Slicit/Roxanne/sources/stl/rev1/X_Carriage_v3.STL

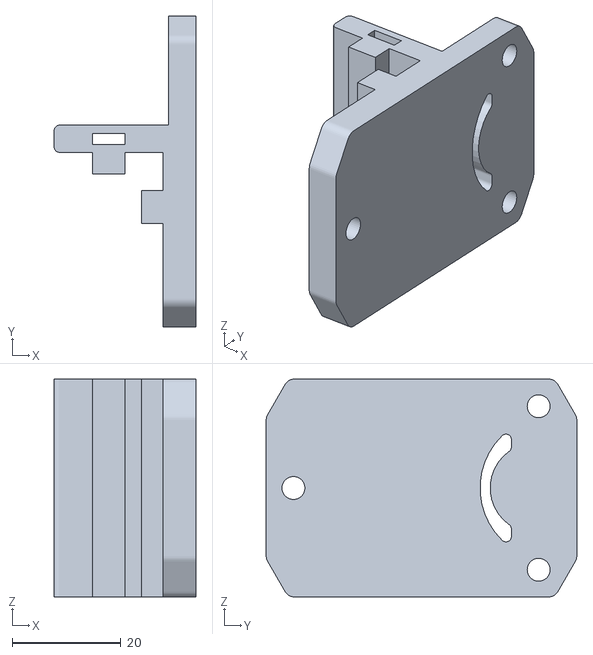
[picture p15: CAD file, 2013-07-26]
sources/stl/rev1/X_Carriage_v3.STL
26.0 x 57.0 x 40.0
