Slicit/Roxanne/sources/solidworks/X-End_Motor_Adj_V2.SLDPRT

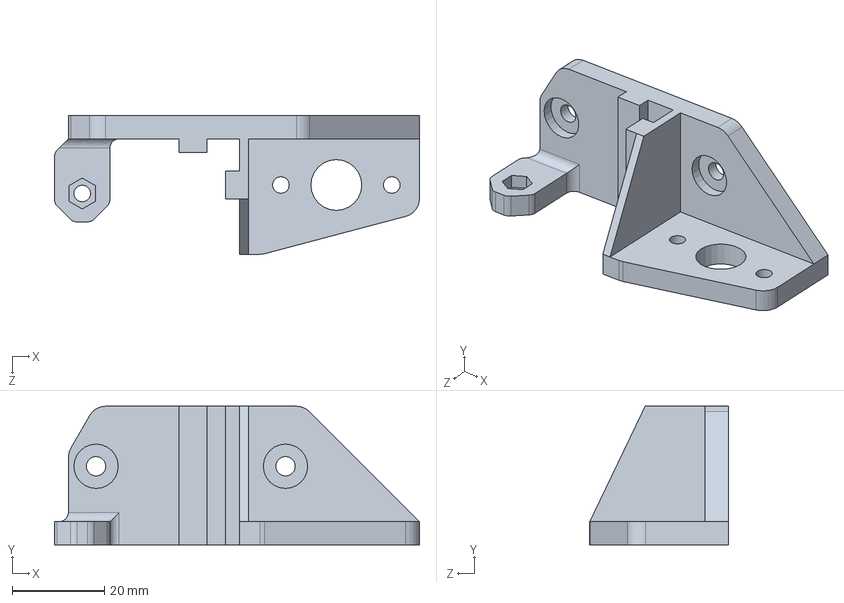
[picture p16: CAD file, 2013-10-02]
sources/solidworks/X-End_Motor_Adj_V2.SLDPRT
79.0 x 30.0 x 30.0 mm
