Slicit/Roxanne/sources/stl/(2)Pulley_T25_624ZZ.stl

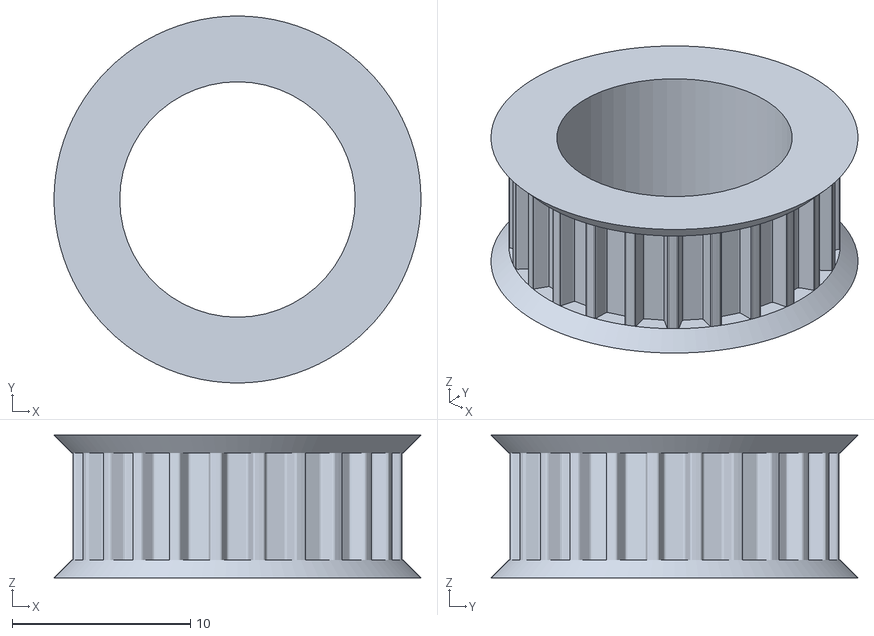
[picture p17: CAD file, 2013-10-02]
sources/stl/(2)Pulley_T25_624ZZ.stl
20.6 x 20.6 x 8.00
