Slicit/Roxanne/sources/stl/rev1/Triple_Fan_Holder.STL

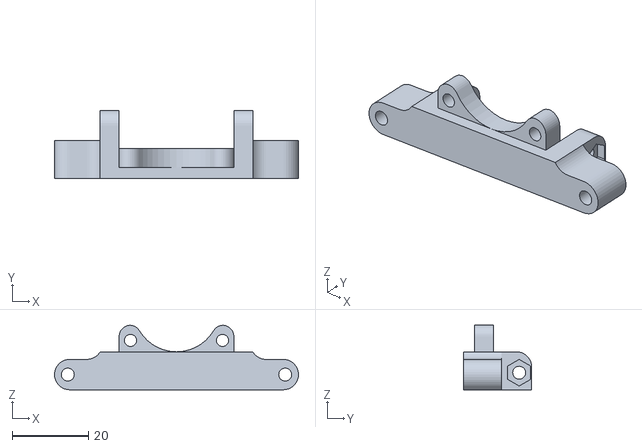
[picture p19: CAD file, 2013-07-26]
sources/stl/rev1/Triple_Fan_Holder.STL
64.2 x 18.0 x 17.0
