Slicit/Roxanne/sources/solidworks/X-End-Idler-V2.SLDPRT

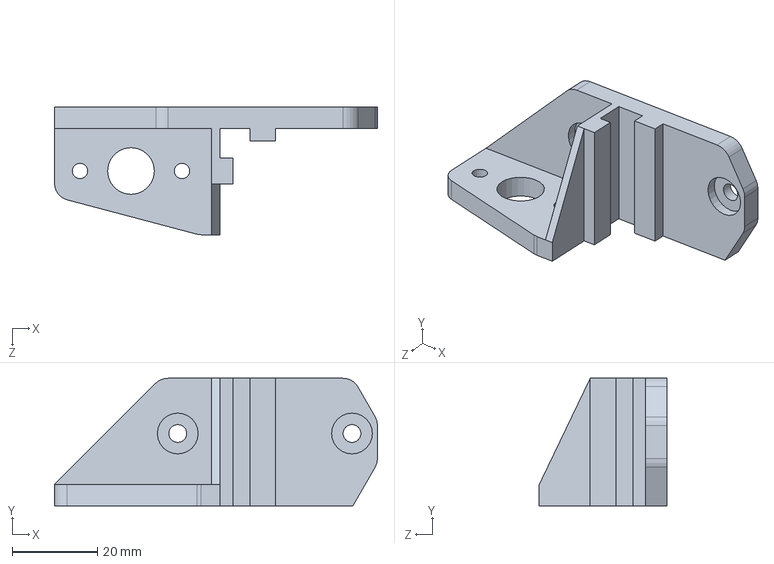
[picture p20: CAD file, 2013-10-02]
sources/solidworks/X-End-Idler-V2.SLDPRT
76.0 x 30.0 x 30.0 mm
