Slicit/Roxanne/sources/stl/rev1/Bowden_JHead_V2.STL

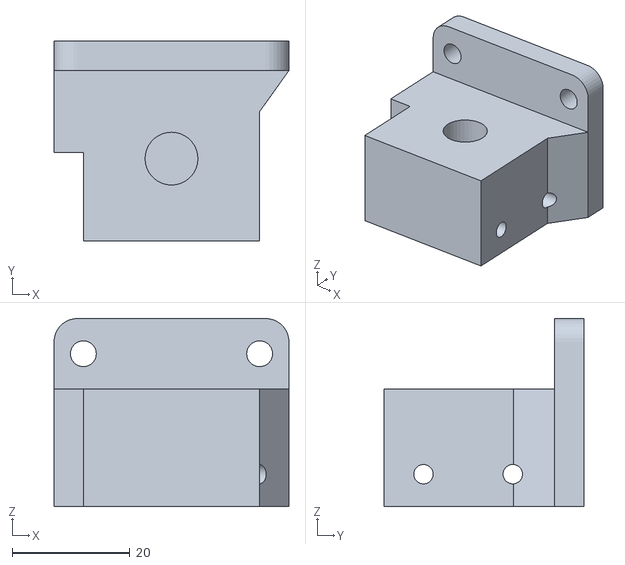
[picture p21: CAD file, 2013-07-26]
sources/stl/rev1/Bowden_JHead_V2.STL
40.0 x 34.0 x 32.0
