Slicit/Roxanne/sources/solidworks/EndstopY.SLDPRT

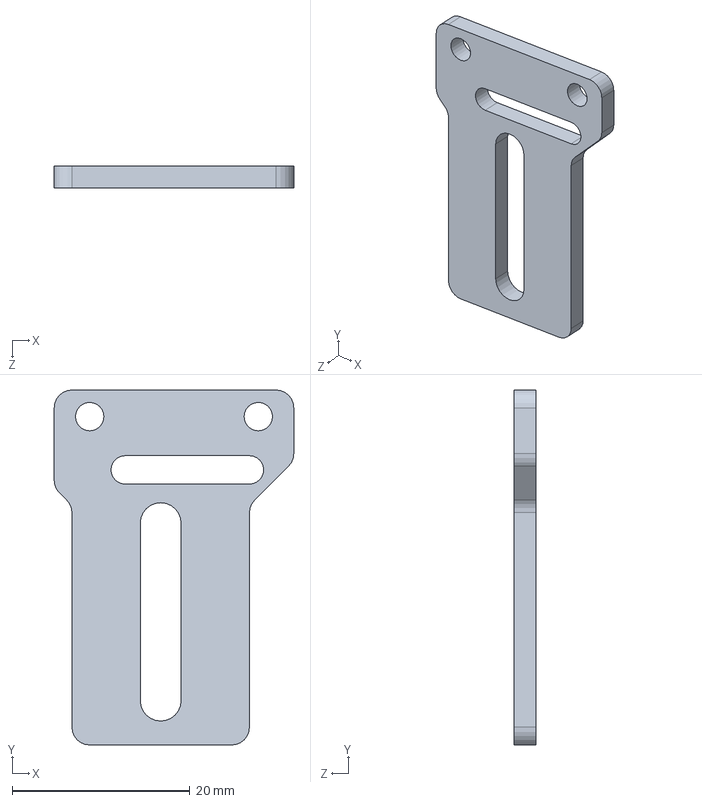
[picture p22: CAD file, 2013-10-02]
sources/solidworks/EndstopY.SLDPRT
27.0 x 40.0 x 2.50 mm
