Slicit/Roxanne/sources/stl/rev1/Glass_Holder.STL

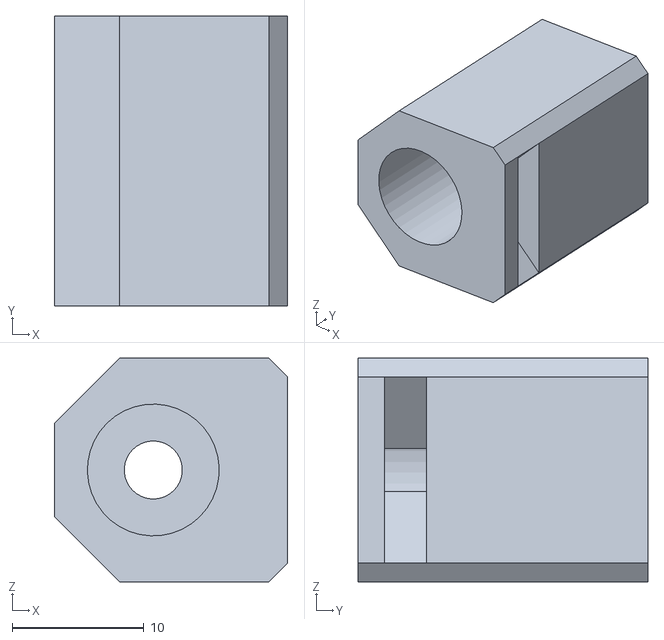
[picture p23: CAD file, 2013-07-24]
sources/stl/rev1/Glass_Holder.STL
17.7 x 22.0 x 17.0
