Slicit/Roxanne/sources/stl/rev1/Axe_Guide_160mm.STL

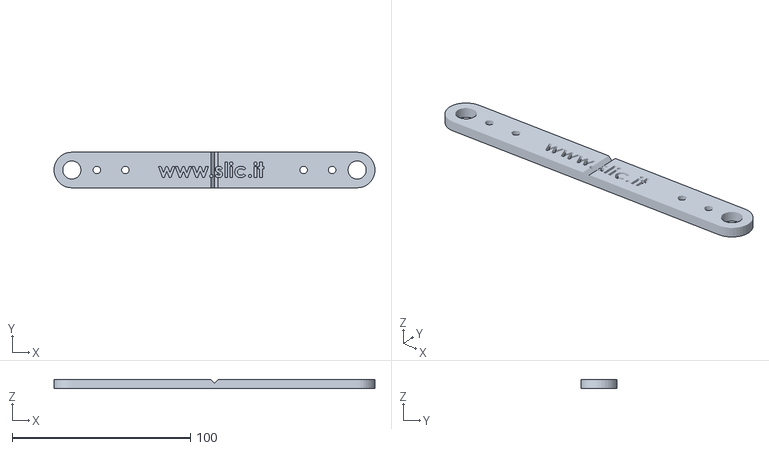
[picture p24: CAD file, 2013-07-24]
sources/stl/rev1/Axe_Guide_160mm.STL
180.0 x 20.0 x 5.00
