Slicit/Roxanne/sources/solidworks/Angle_Holder.SLDPRT

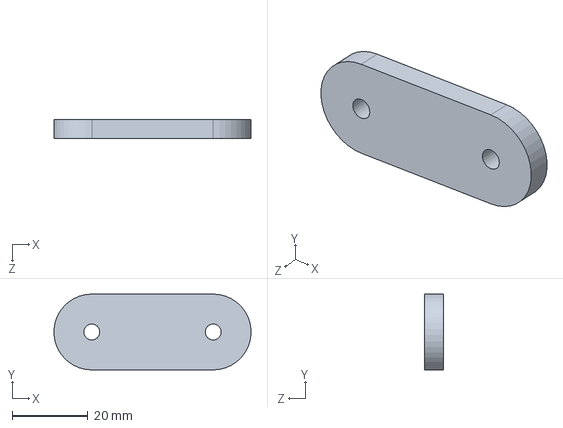
[picture p25: CAD file, 2013-09-25]
sources/solidworks/Angle_Holder.SLDPRT
51.9 x 20.0 x 5.00 mm
