Slicit/Roxanne/sources/stl/(1)Y-Endstop-Holder.STL

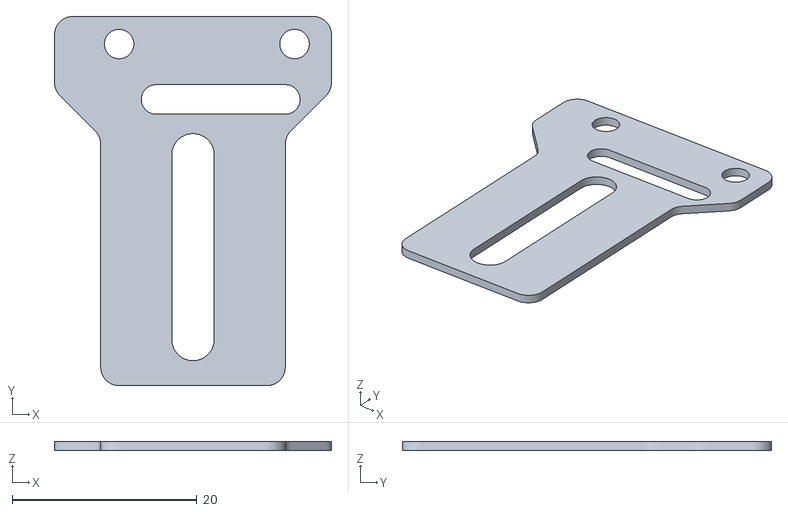
[picture p26: CAD file, 2013-09-25]
sources/stl/(1)Y-Endstop-Holder.STL
30.0 x 40.0 x 1.00
