Slicit/Roxanne/sources/stl/rev1/Y_Motor_Bottom.STL

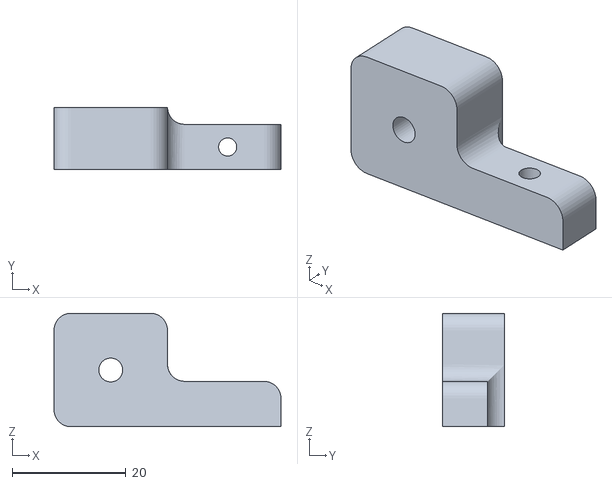
[picture p27: CAD file, 2013-07-10]
sources/stl/rev1/Y_Motor_Bottom.STL
40.0 x 11.0 x 20.0
