Slicit/Roxanne/sources/solidworks/Charn_Type_1.SLDPRT

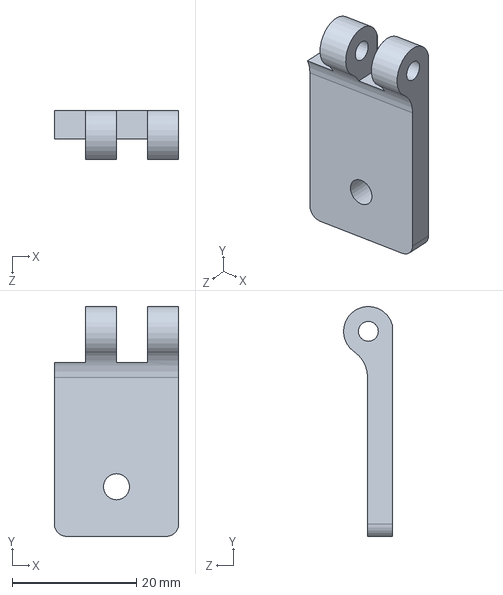
[picture p28: CAD file, 2013-09-25]
sources/solidworks/Charn_Type_1.SLDPRT
20.0 x 37.0 x 7.87 mm
