Slicit/Roxanne/sources/stl/(8)Nut_Holder_Leveller.STL

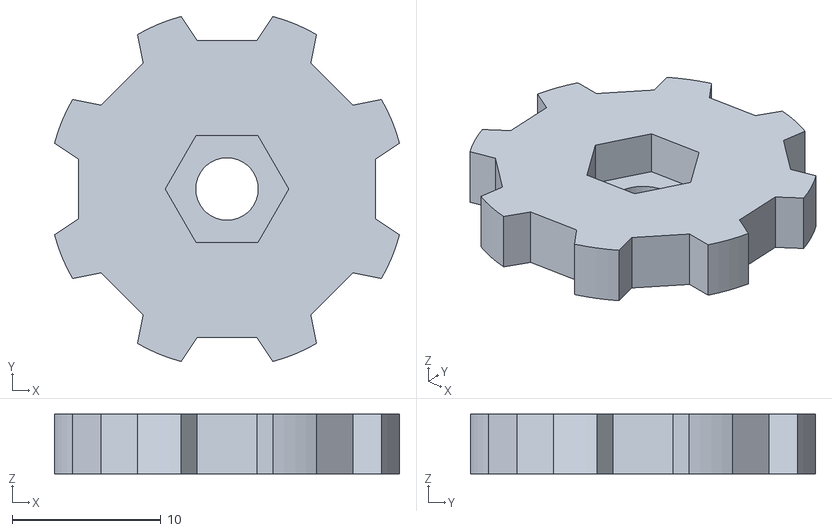
[picture p29: CAD file, 2013-09-25]
sources/stl/(8)Nut_Holder_Leveller.STL
23.2 x 23.2 x 4.00
