Slicit/Roxanne/sources/stl/rev1/Y_Motor_Top.STL

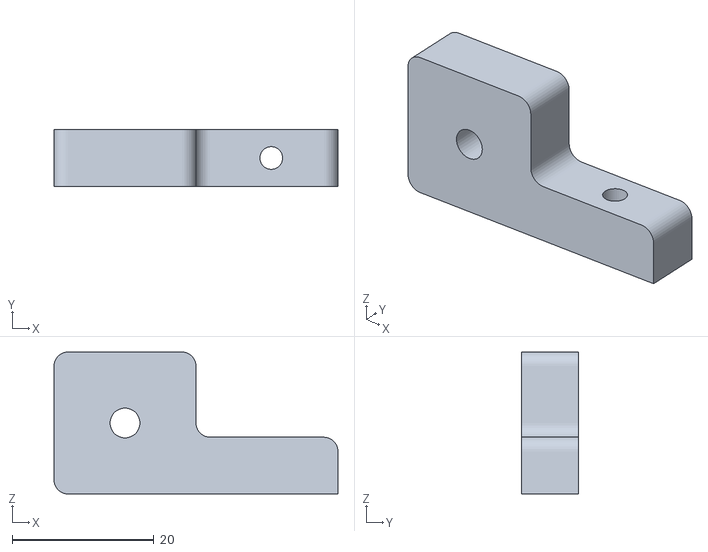
[picture p30: CAD file, 2013-07-10]
sources/stl/rev1/Y_Motor_Top.STL
40.0 x 8.00 x 20.0
