Slicit/Roxanne/sources/solidworks/Spacer_Y_Endstop_2.SLDPRT

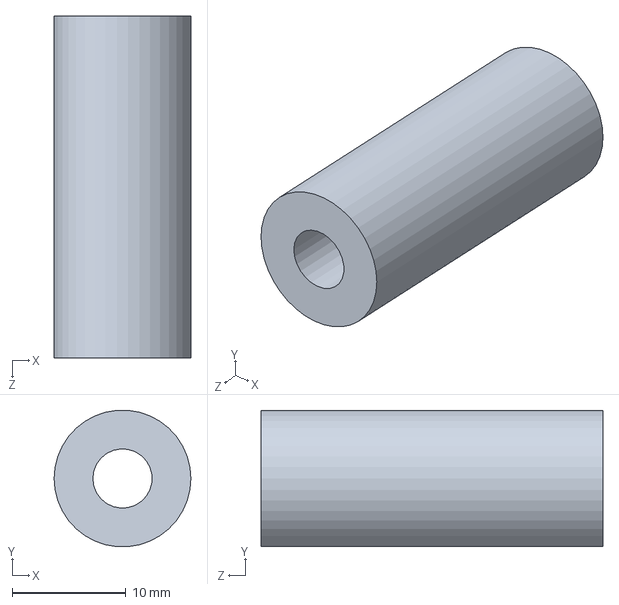
[picture p31: CAD file, 2013-09-25]
sources/solidworks/Spacer_Y_Endstop_2.SLDPRT
12.0 x 12.0 x 30.0 mm
