Slicit/Roxanne/sources/stl/(4)Glass_Holder.STL

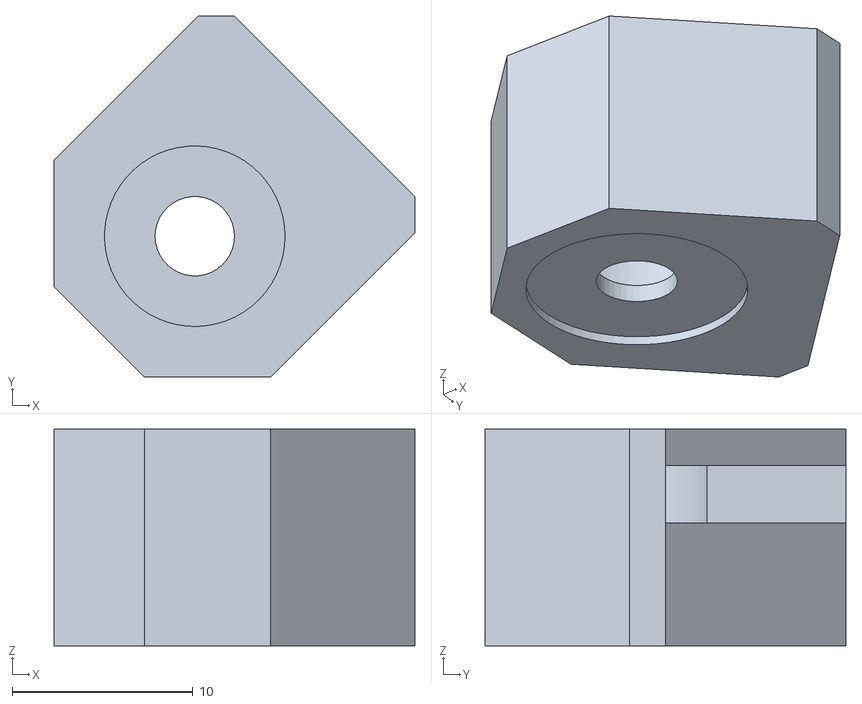
[picture p32: CAD file, 2013-09-25]
sources/stl/(4)Glass_Holder.STL
20.0 x 20.0 x 12.0
