Slicit/Roxanne/sources/stl/(1)X-Carriage.STL

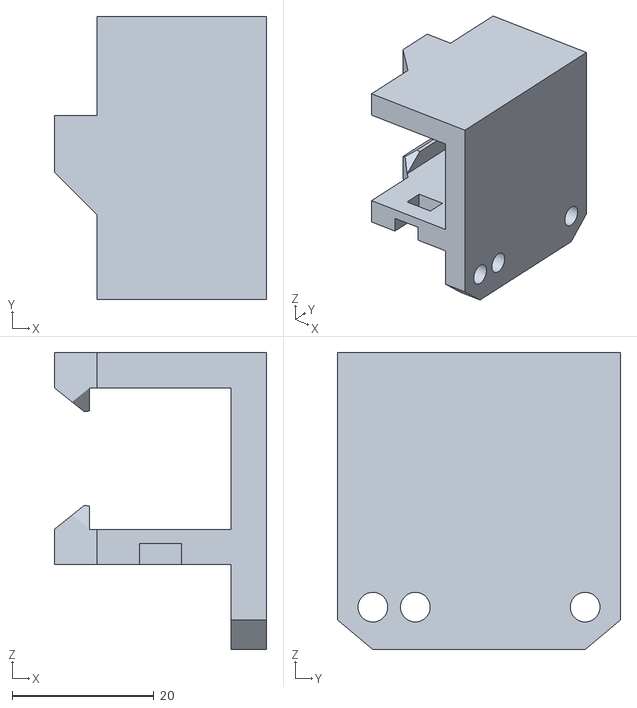
[picture p33: CAD file, 2013-09-25]
sources/stl/(1)X-Carriage.STL
30.0 x 40.0 x 42.0
