Slicit/Roxanne/sources/stl/(1)Y-Endstop-Spacer.STL

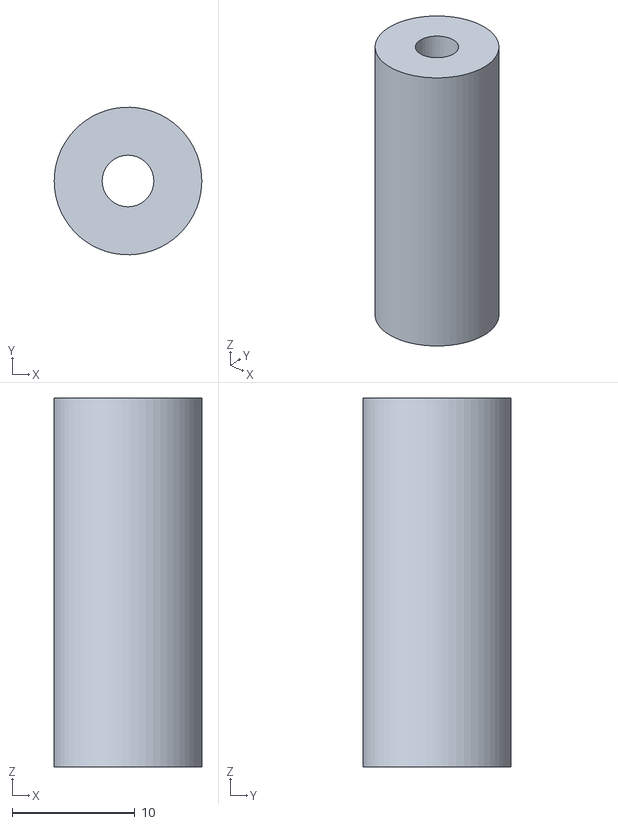
[picture p34: CAD file, 2013-09-25]
sources/stl/(1)Y-Endstop-Spacer.STL
12.0 x 12.0 x 30.0
