Slicit/Roxanne/sources/stl/rev1/LM10UU_Holder_Higher.STL

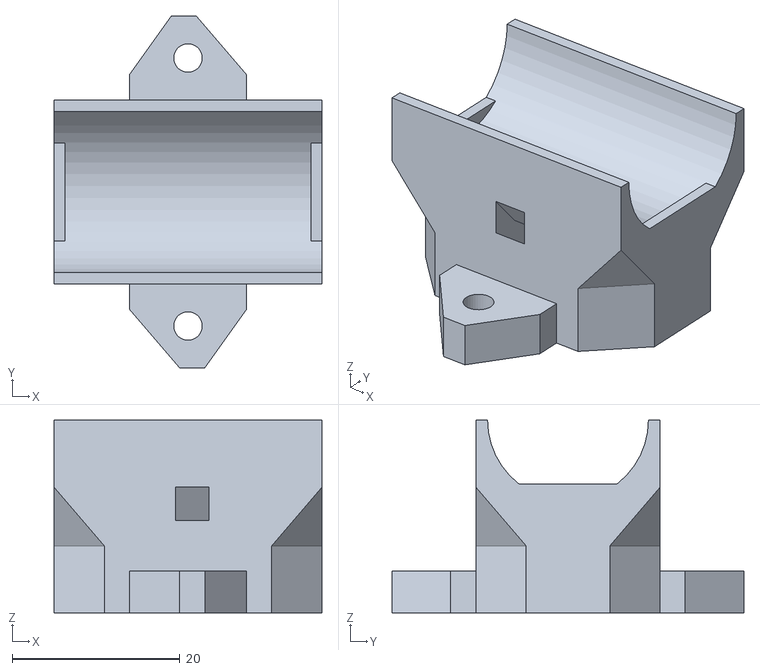
[picture p35: CAD file, 2013-06-12]
sources/stl/rev1/LM10UU_Holder_Higher.STL
32.0 x 42.0 x 23.0
