Slicit/Roxanne/sources/stl/(1)X-Endstop-Holder.STL

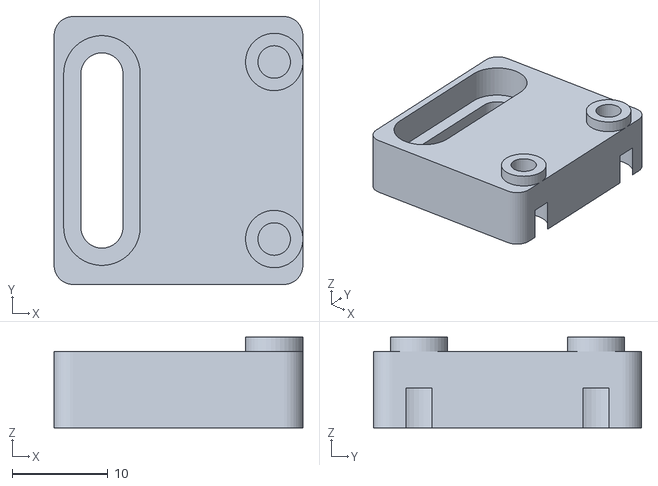
[picture p36: CAD file, 2013-09-25]
sources/stl/(1)X-Endstop-Holder.STL
26.0 x 28.0 x 9.50
