Slicit/Roxanne/sources/stl/rev1/Axe_Guide_160mm_Bearing.STL

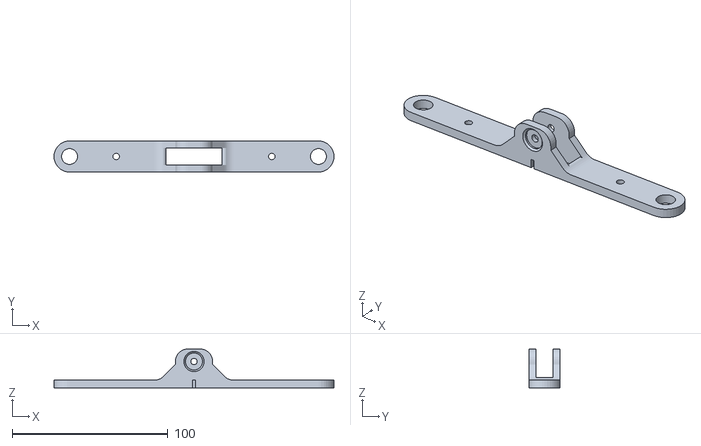
[picture p37: CAD file, 2013-06-12]
sources/stl/rev1/Axe_Guide_160mm_Bearing.STL
180.0 x 20.0 x 25.0
