Slicit/Roxanne/sources/stl/Fans.STL

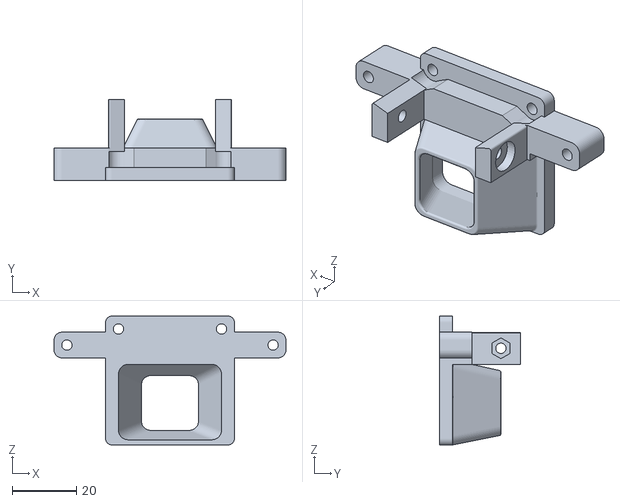
[picture p38: CAD file, 2013-09-23]
sources/stl/Fans.STL
72.0 x 25.0 x 40.0
