Slicit/Roxanne/sources/solidworks/Nema17_48mm.SLDPRT

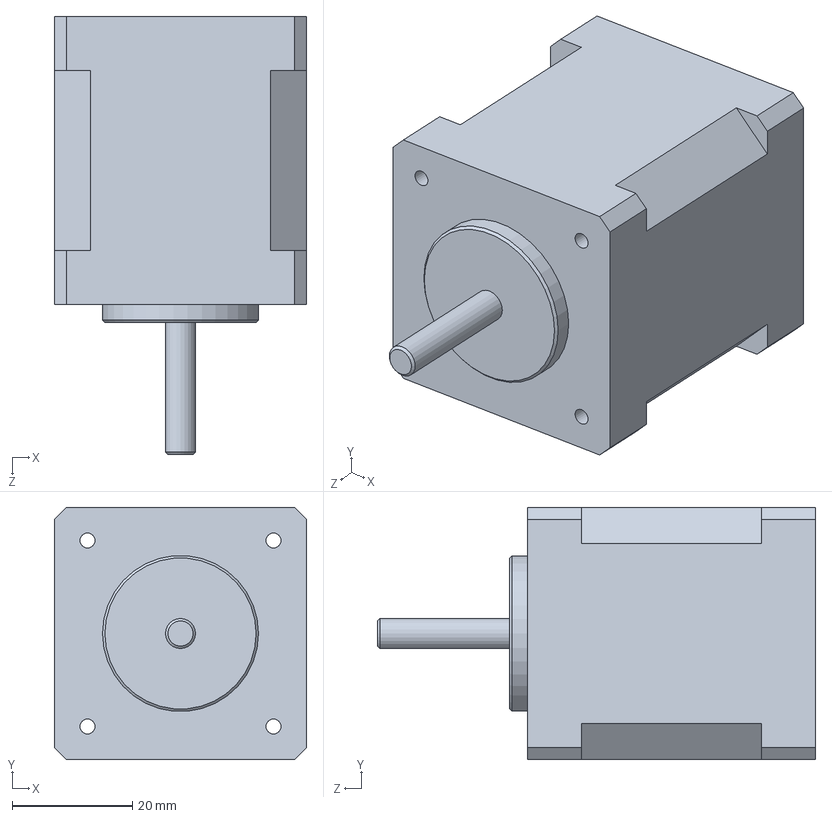
[picture p39: CAD file, 2013-09-25]
sources/solidworks/Nema17_48mm.SLDPRT
42.0 x 42.0 x 73.0 mm
