Slicit/Roxanne/sources/stl/(1)Power-Switch-Plate.STL

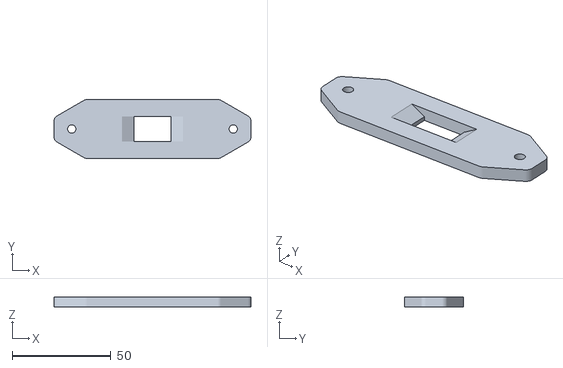
[picture p40: CAD file, 2013-09-23]
sources/stl/(1)Power-Switch-Plate.STL
100.0 x 30.0 x 5.00
