Slicit/Roxanne/sources/stl/rev1/Direct_Drive_Extruder_v3.STL

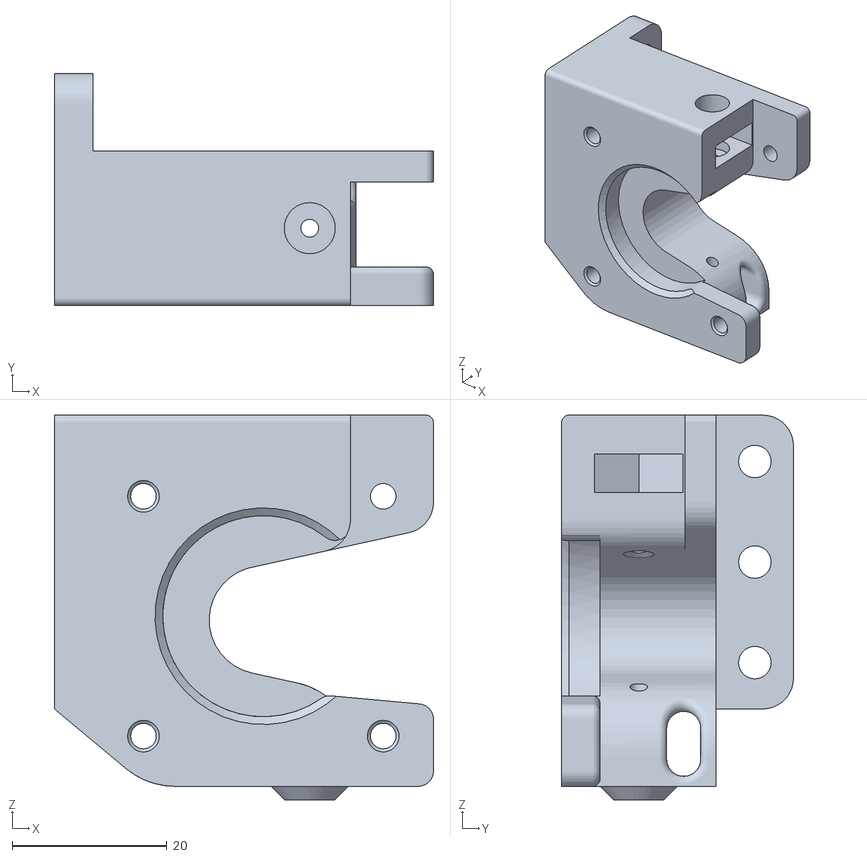
[picture p41: CAD file, 2013-06-11]
sources/stl/rev1/Direct_Drive_Extruder_v3.STL
49.0 x 30.0 x 49.8
