Slicit/Roxanne/sources/stl/rev1/Fan_Support_40mm_Model_2.STL

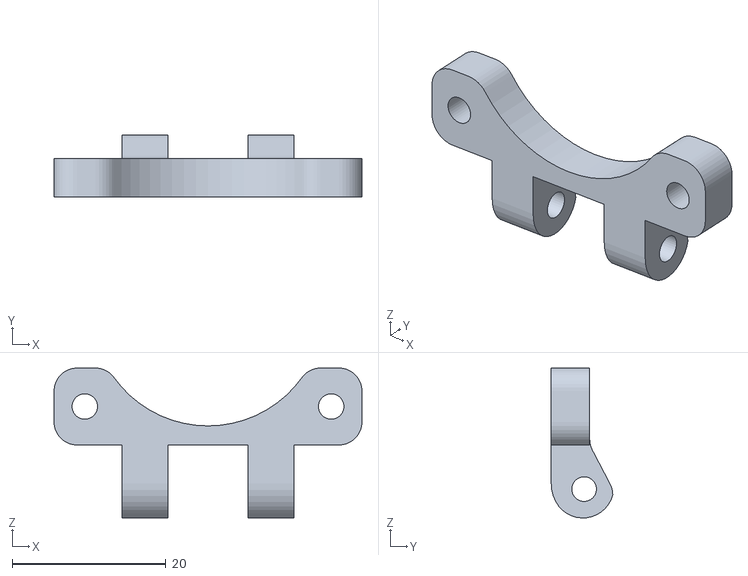
[picture p42: CAD file, 2013-05-20]
sources/stl/rev1/Fan_Support_40mm_Model_2.STL
40.0 x 8.00 x 19.5
