Slicit/Roxanne/sources/stl/rev1/Fan_Support_40mm_Model_1.STL

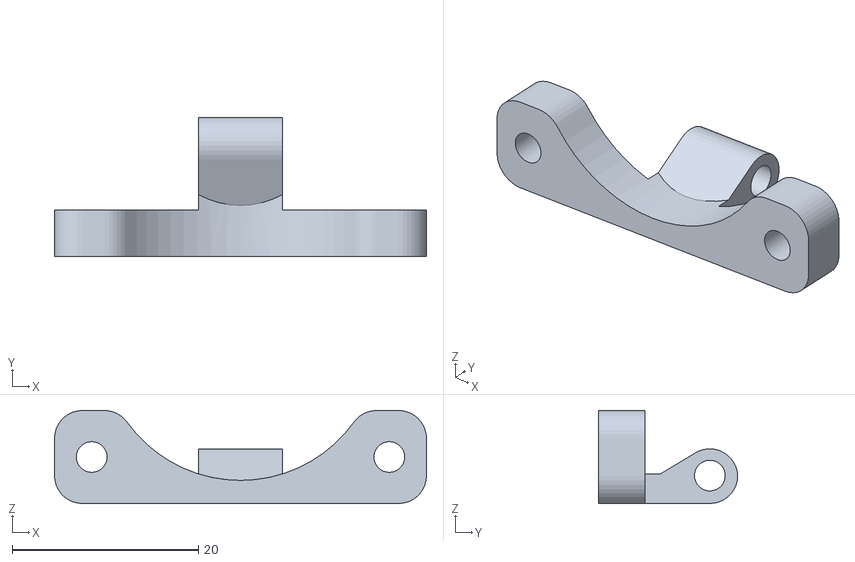
[picture p43: CAD file, 2013-05-20]
sources/stl/rev1/Fan_Support_40mm_Model_1.STL
40.0 x 15.0 x 10.00
