Slicit/Roxanne/sources/solidworks/X-End-Motor-V1.SLDPRT

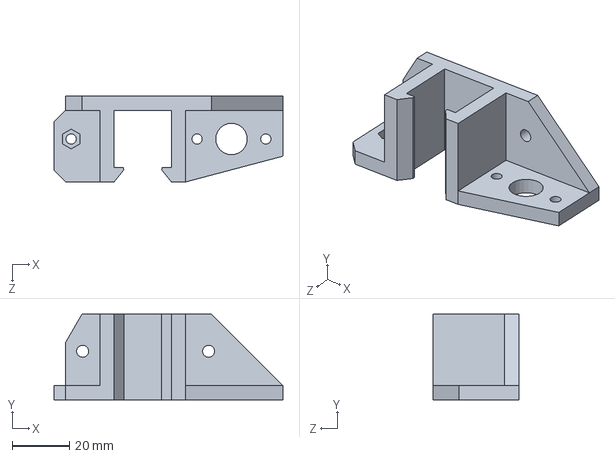
[picture p44: CAD file, 2013-09-25]
sources/solidworks/X-End-Motor-V1.SLDPRT
80.0 x 30.0 x 30.0 mm
