Slicit/Roxanne/sources/stl/rev1/Dual_Extruder_Jhead.stl

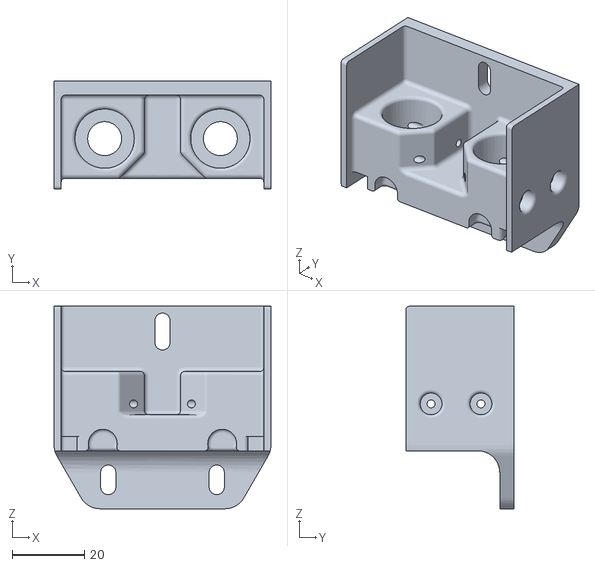
[picture p45: CAD file, 2013-05-20]
sources/stl/rev1/Dual_Extruder_Jhead.stl
60.0 x 30.0 x 56.0
