Slicit/Roxanne/sources/stl/rev1/Fan_Holder.STL

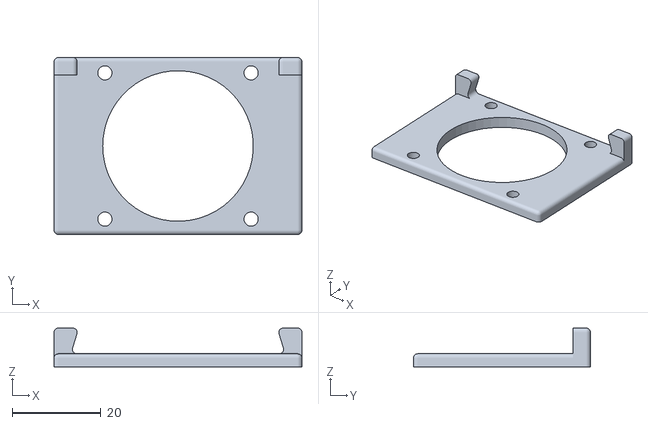
[picture p46: CAD file, 2013-05-20]
sources/stl/rev1/Fan_Holder.STL
56.0 x 40.0 x 8.80
