Slicit/Roxanne/sources/solidworks/Fan_40mm.SLDPRT

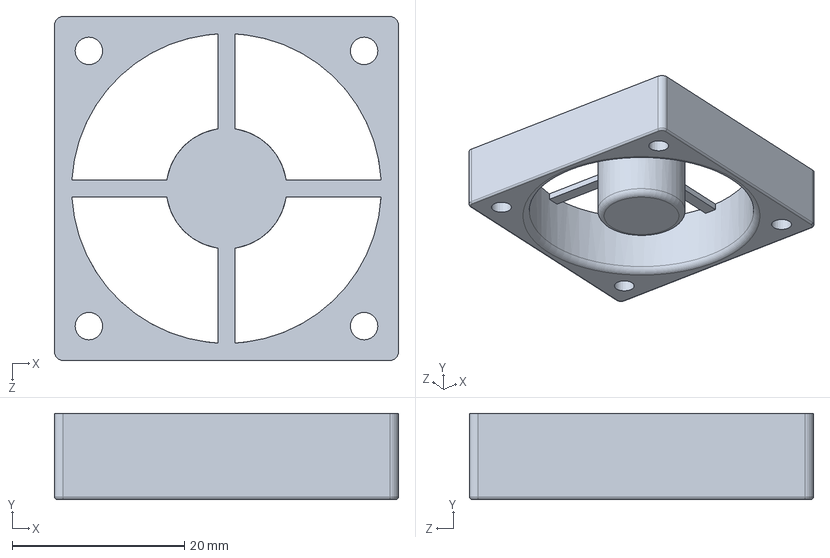
[picture p47: CAD file, 2013-09-23]
sources/solidworks/Fan_40mm.SLDPRT
40.0 x 10.0 x 40.0 mm
