Slicit/Roxanne/sources/stl/rev1/Direct_Drive_Tightner.stl

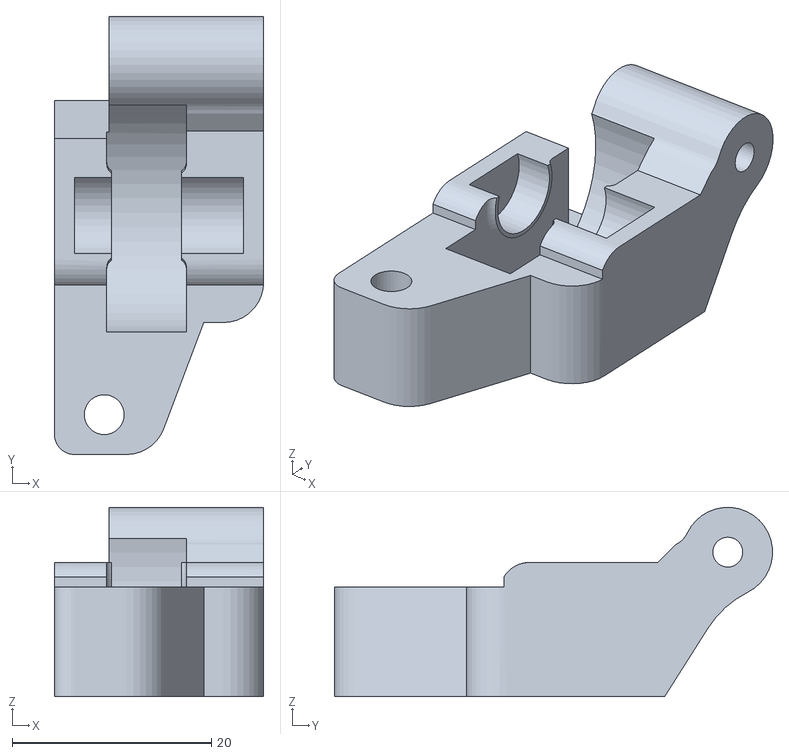
[picture p48: CAD file, 2013-05-19]
sources/stl/rev1/Direct_Drive_Tightner.stl
21.0 x 44.0 x 19.0
