Slicit/Roxanne/sources/solidworks/Mirror_Build_Plate.SLDPRT

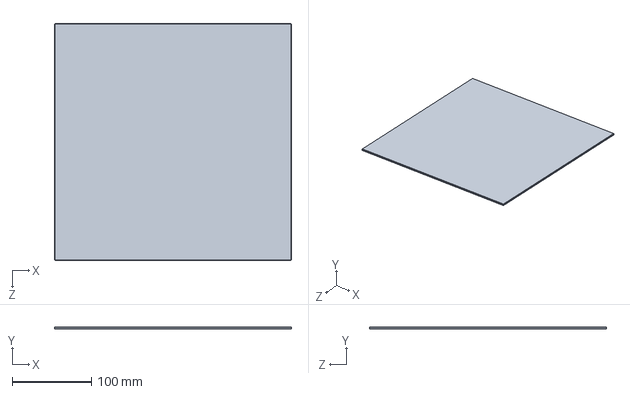
[picture p49: CAD file, 2013-09-23]
sources/solidworks/Mirror_Build_Plate.SLDPRT
300.0 x 3.00 x 300.0 mm
