Slicit/Roxanne/sources/stl/rev1/Rotary_LCD.STL

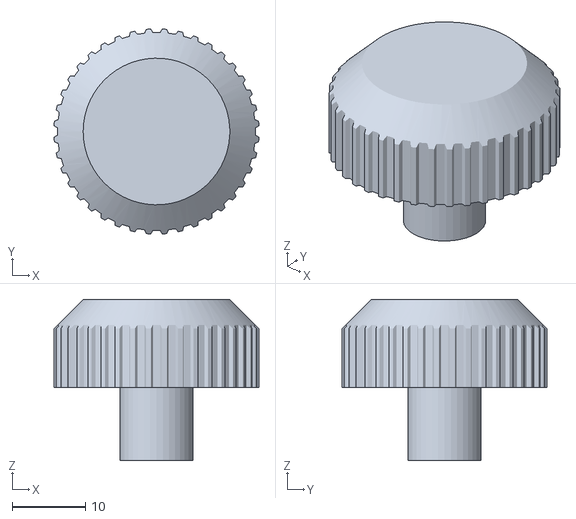
[picture p50: CAD file, 2013-05-19]
sources/stl/rev1/Rotary_LCD.STL
28.0 x 28.0 x 22.0
