Slicit/Roxanne/sources/stl/rev1/X_End_Idler.STL

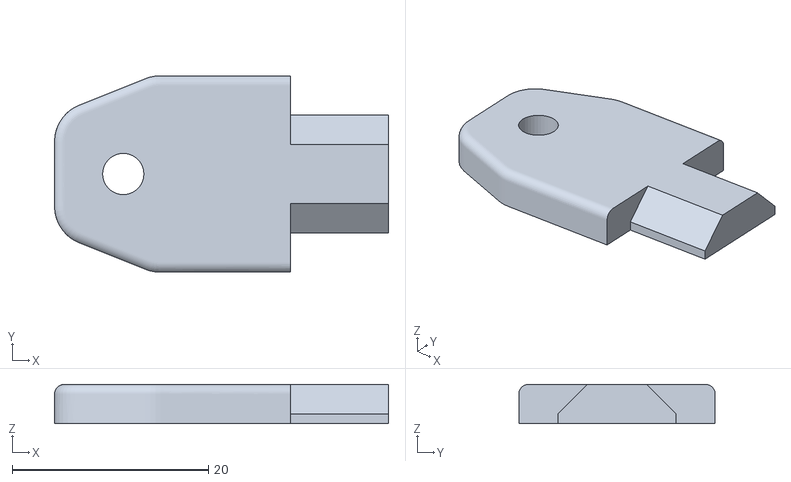
[picture p51: CAD file, 2013-05-19]
sources/stl/rev1/X_End_Idler.STL
34.0 x 20.0 x 4.00
