Slicit/Roxanne/sources/stl/rev1/X_Motor_Plate.STL

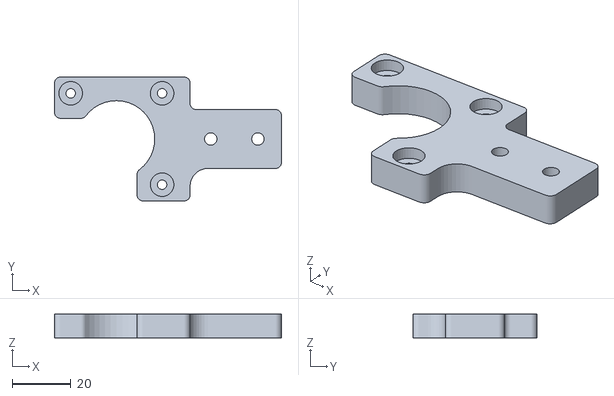
[picture p52: CAD file, 2013-05-18]
sources/stl/rev1/X_Motor_Plate.STL
77.0 x 42.0 x 8.00
