Slicit/Roxanne/sources/stl/rev1/Endstop_Nopcb_Holder_Profile_Y.STL

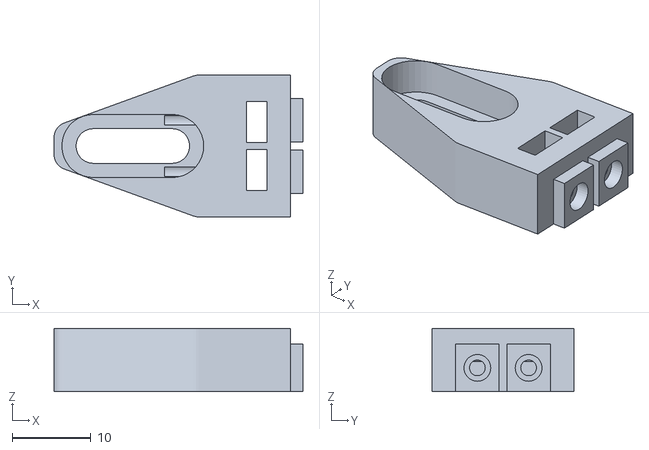
[picture p53: CAD file, 2013-05-15]
sources/stl/rev1/Endstop_Nopcb_Holder_Profile_Y.STL
31.6 x 18.0 x 8.00
