Slicit/Roxanne/sources/stl/rev1/Endstop_Nopcb_Holder_Profile_XZ.STL

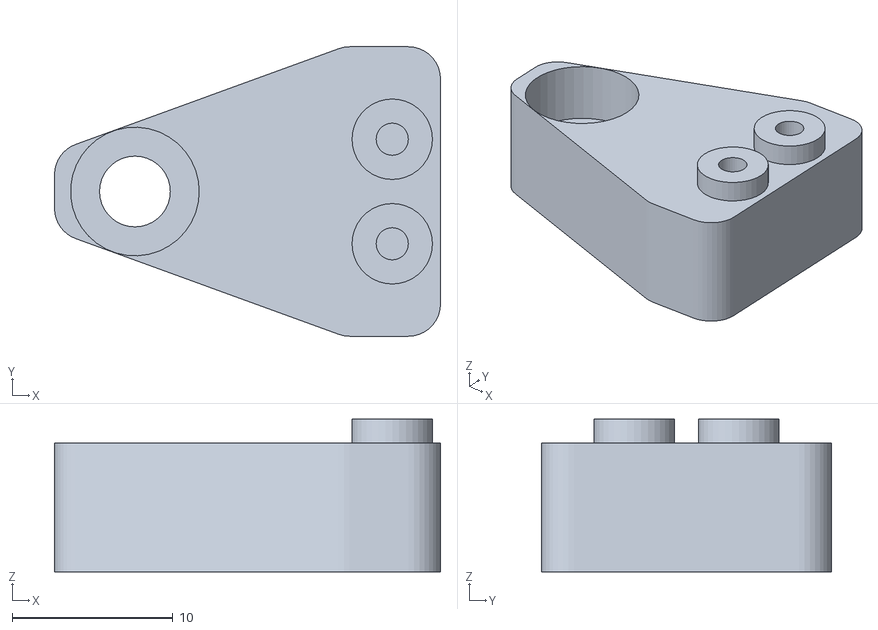
[picture p54: CAD file, 2013-05-15]
sources/stl/rev1/Endstop_Nopcb_Holder_Profile_XZ.STL
24.0 x 18.0 x 9.50
