Slicit/Roxanne/sources/stl/rev1/Spacer.STL

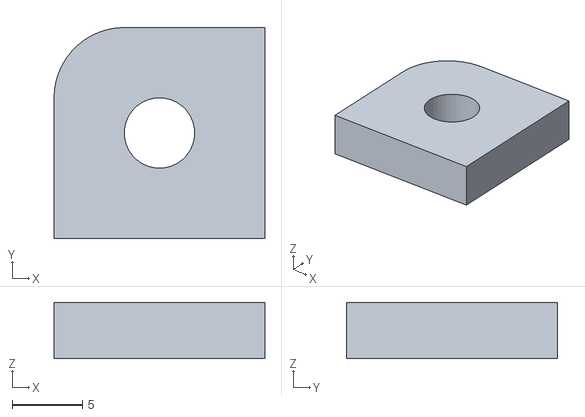
[picture p57: CAD file, 2013-05-12]
sources/stl/rev1/Spacer.STL
15.0 x 15.0 x 4.00
