Slicit/Roxanne/sources/stl/rev1/Angle_33.STL

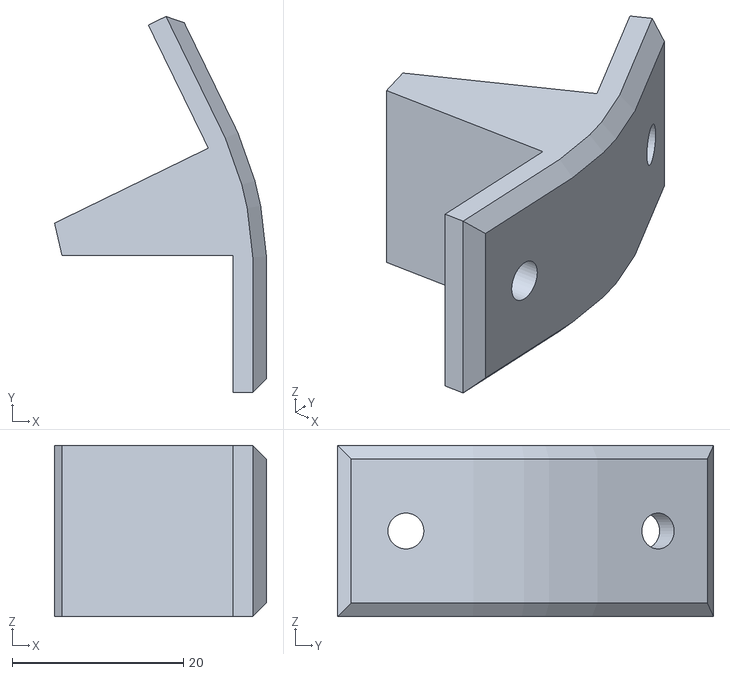
[picture p58: CAD file, 2013-05-11]
sources/stl/rev1/Angle_33.STL
24.8 x 44.0 x 20.0
