Slicit/Roxanne/sources/stl/rev1/LM10UU_Holder.STL

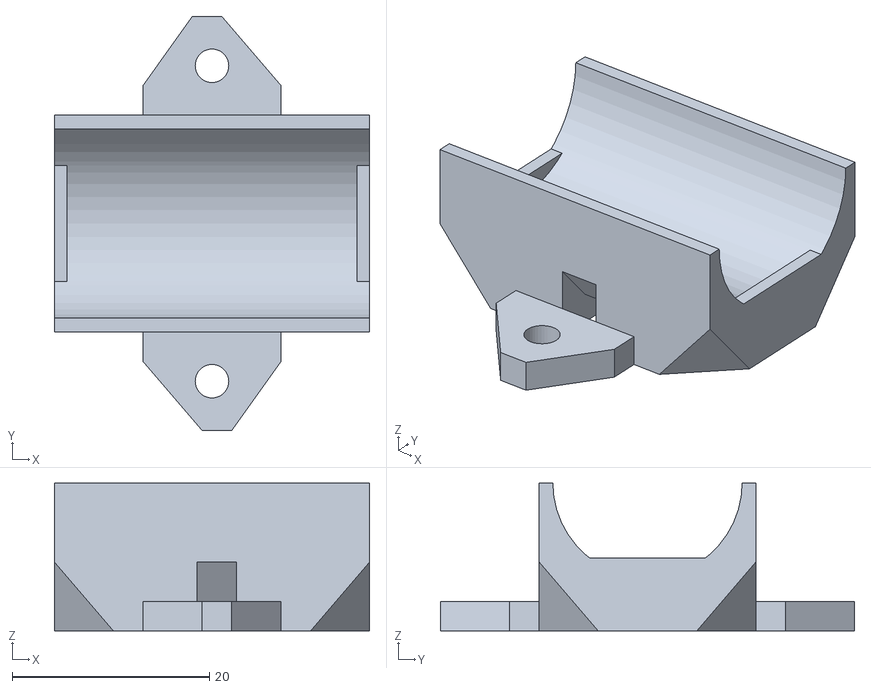
[picture p59: CAD file, 2013-05-11]
sources/stl/rev1/LM10UU_Holder.STL
32.0 x 42.0 x 15.0
