Slicit/Roxanne/sources/stl/rev1/Angle_57.stl

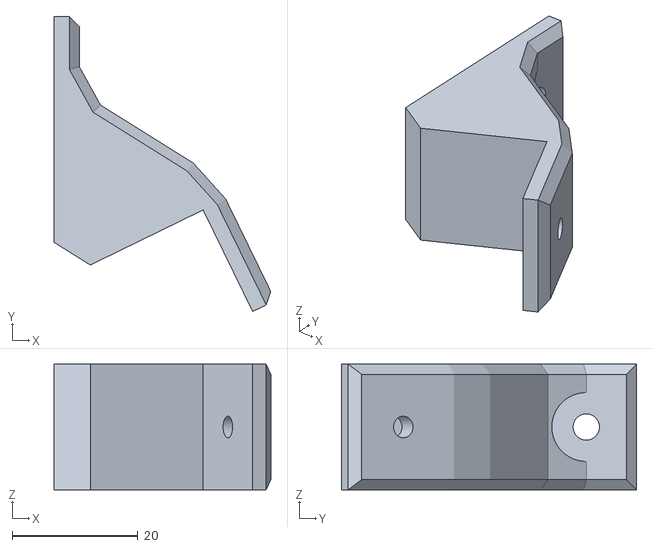
[picture p60: CAD file, 2013-05-11]
sources/stl/rev1/Angle_57.stl
34.5 x 47.0 x 20.0
