Slicit/Roxanne/sources/solidworks/Wood_Bed_Simplified.SLDPRT

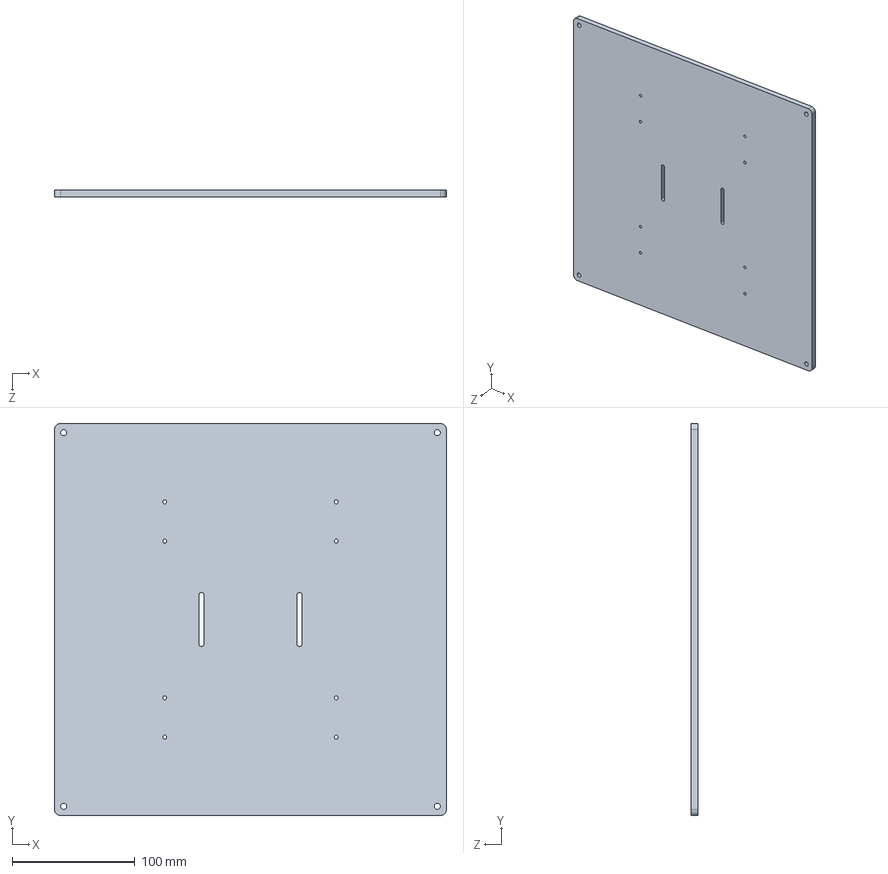
[picture p61: CAD file, 2013-08-12]
sources/solidworks/Wood_Bed_Simplified.SLDPRT
320.0 x 320.0 x 6.00 mm
