Slicit/Roxanne/sources/stl/rev1/Spool_Holder.STL

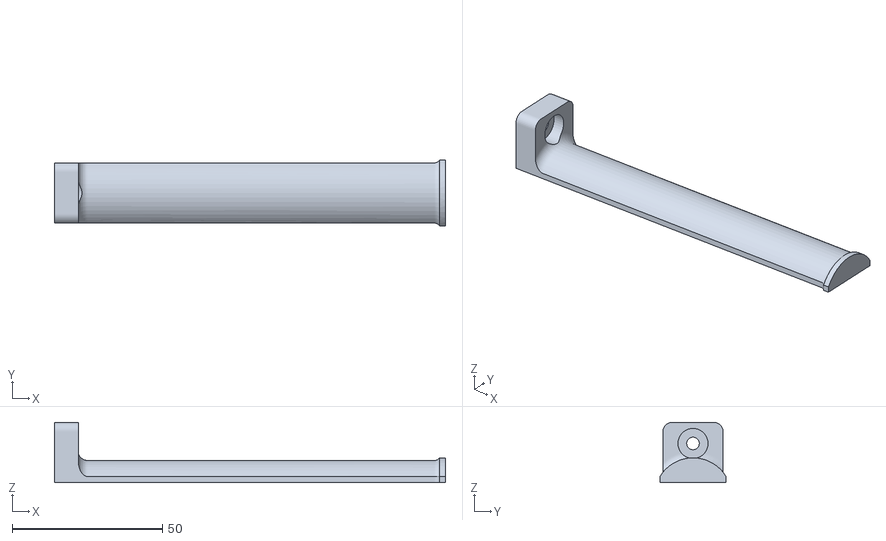
[picture p62: CAD file, 2013-05-11]
sources/stl/rev1/Spool_Holder.STL
130.0 x 22.0 x 20.0
