Slicit/Roxanne/sources/stl/rev1/YZ_Motor_Plate.STL

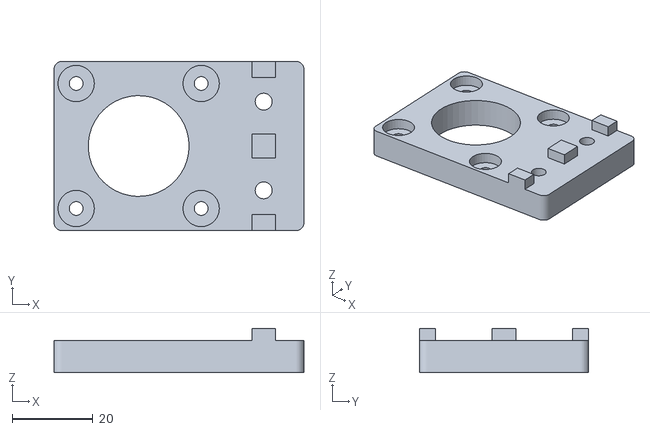
[picture p63: CAD file, 2013-05-11]
sources/stl/rev1/YZ_Motor_Plate.STL
62.0 x 42.0 x 11.0
