Slicit/Roxanne/sources/solidworks/Profil_Alu_20x20_2-120mm.SLDPRT

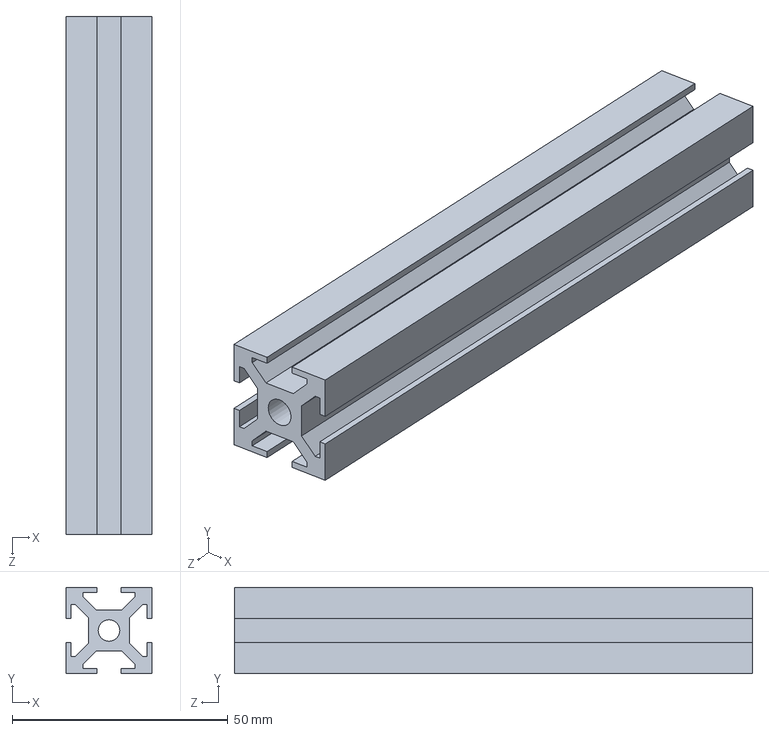
[picture p64: CAD file, 2013-06-11]
sources/solidworks/Profil_Alu_20x20_2-120mm.SLDPRT
20.0 x 20.0 x 120.0 mm
