Slicit/Roxanne/sources/solidworks/LM10UU.SLDPRT

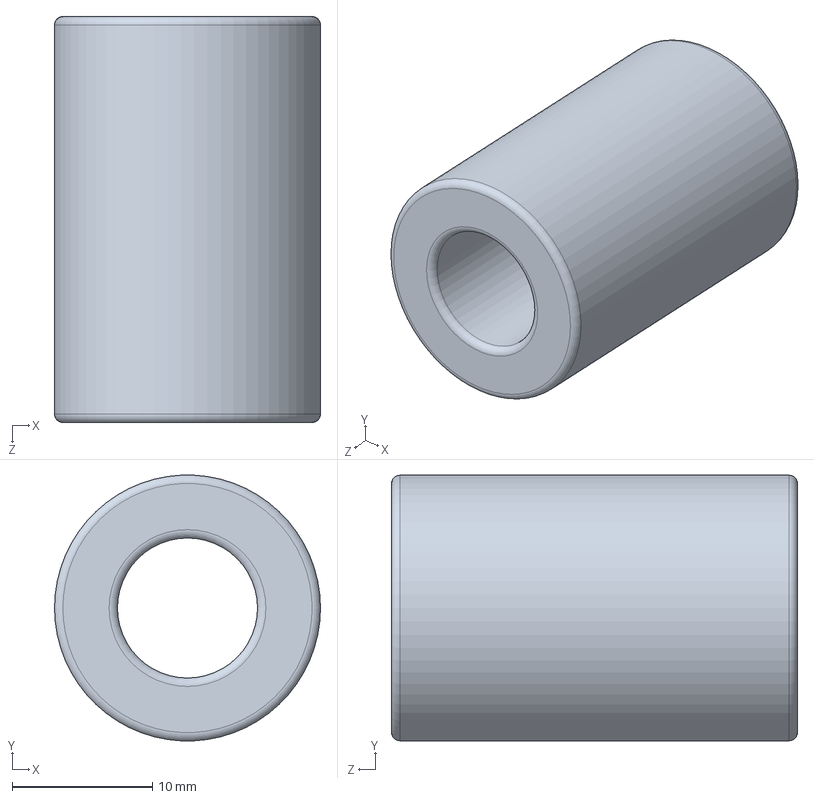
[picture p65: CAD file, 2013-05-19]
sources/solidworks/LM10UU.SLDPRT
19.0 x 19.0 x 29.0 mm
