Slicit/Roxanne/sources/solidworks/Reset_Button.SLDPRT

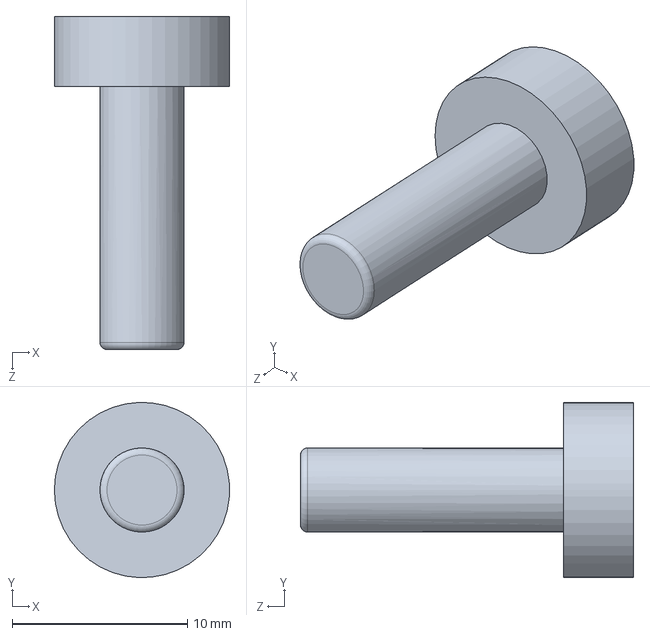
[picture p66: CAD file, 2013-05-19]
sources/solidworks/Reset_Button.SLDPRT
10.0 x 9.99 x 19.0 mm
