Slicit/Roxanne/sources/solidworks/Pneufit_4mm_OD.SLDPRT

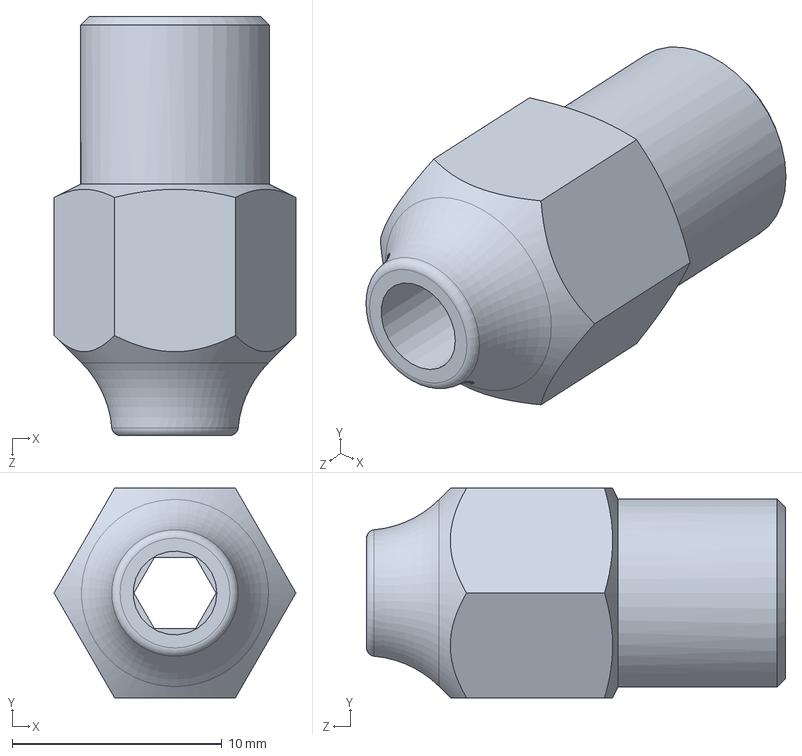
[picture p67: CAD file, 2013-05-19]
sources/solidworks/Pneufit_4mm_OD.SLDPRT
11.5 x 10.0 x 20.0 mm
