Slicit/Roxanne/sources/solidworks/RRD_LCD_Smart_Controller.sldprt

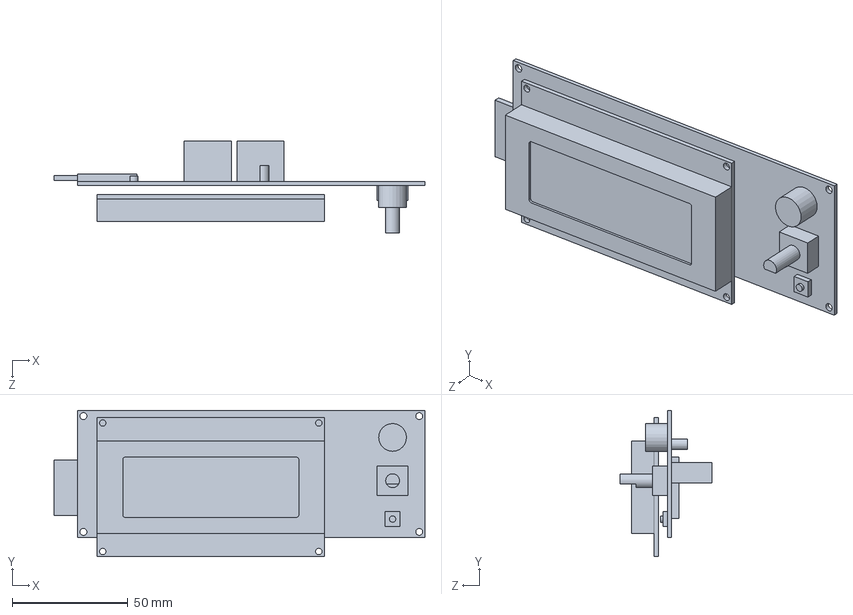
[picture p68: CAD file, 2013-05-19]
sources/solidworks/RRD_LCD_Smart_Controller.sldprt
160.2 x 63.2 x 39.6 mm
