Slicit/Roxanne/sources/solidworks/JHead_MKVB.SLDPRT

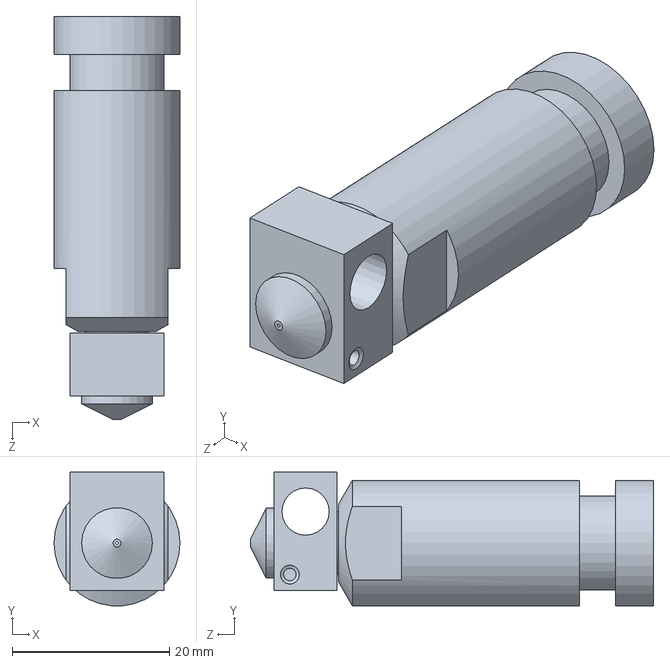
[picture p69: CAD file, 2013-05-19]
sources/solidworks/JHead_MKVB.SLDPRT
16.0 x 17.0 x 51.2 mm
