Slicit/Roxanne/sources/solidworks/Angle_2040.SLDPRT

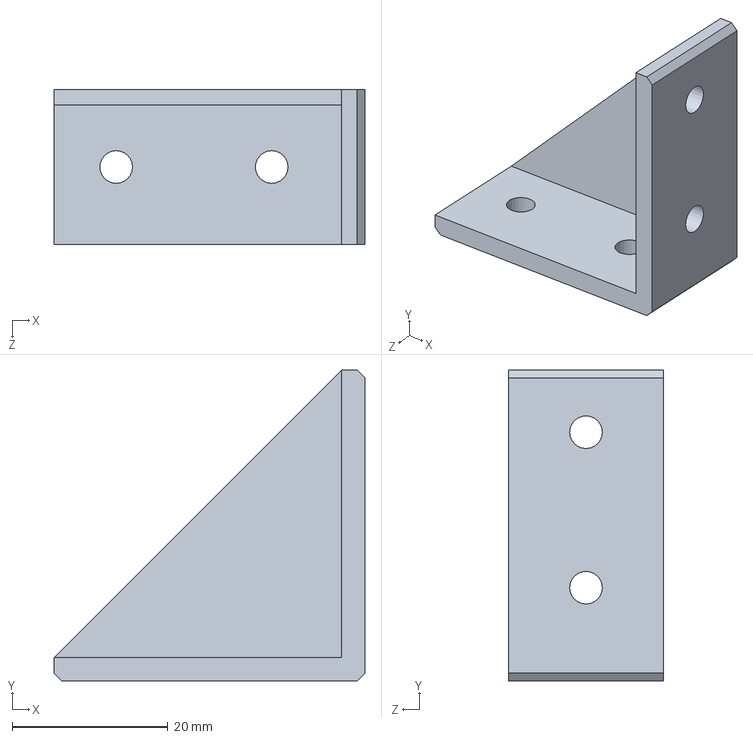
[picture p70: CAD file, 2013-05-18]
sources/solidworks/Angle_2040.SLDPRT
40.0 x 40.0 x 20.0 mm
