Slicit/Roxanne/sources/solidworks/Idler_624.SLDPRT

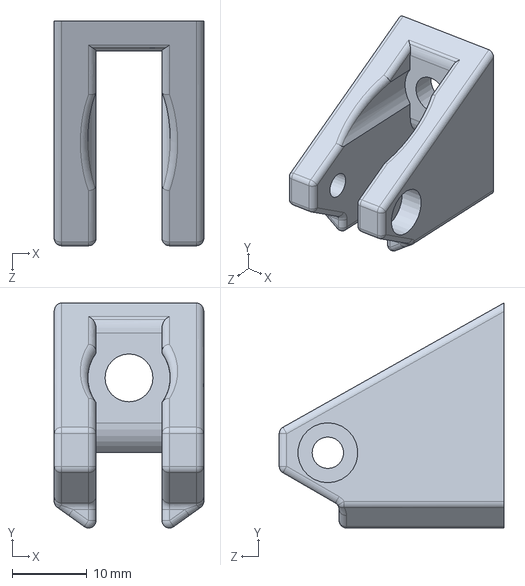
[picture p71: CAD file, 2013-05-15]
sources/solidworks/Idler_624.SLDPRT
20.0 x 30.1 x 30.0 mm
