Slicit/Roxanne/sources/solidworks/LCD_Plate.SLDPRT

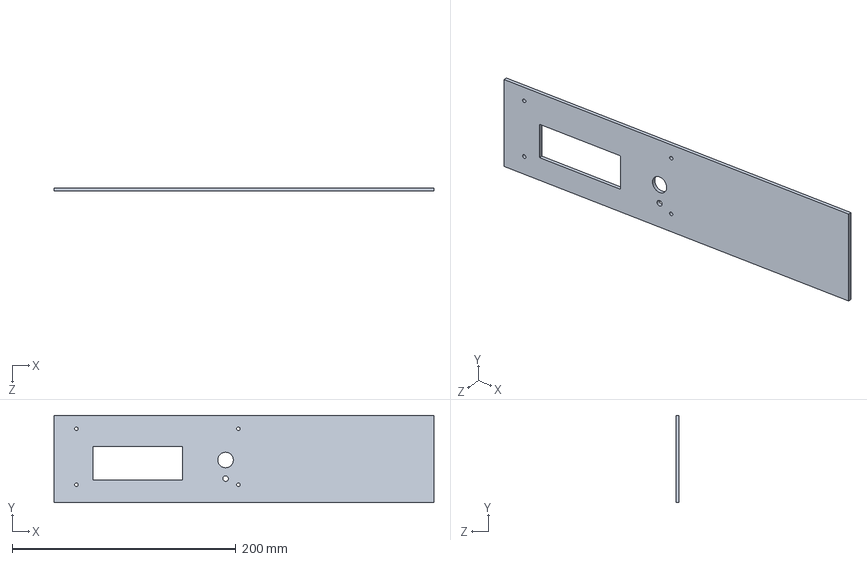
[picture p72: CAD file, 2013-05-12]
sources/solidworks/LCD_Plate.SLDPRT
340.0 x 78.0 x 3.00 mm
