Slicit/Roxanne/sources/solidworks/Profil_Alu_20x20_Default.SLDPRT

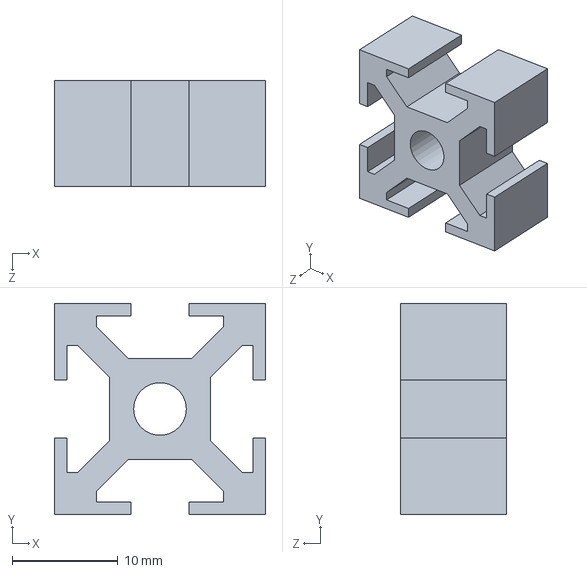
[picture p73: CAD file, 2013-05-11]
sources/solidworks/Profil_Alu_20x20_Default.SLDPRT
20.0 x 20.0 x 10.0 mm
