Slicit/Roxanne/sources/solidworks/Profil_Alu_20x20_100mm.SLDPRT

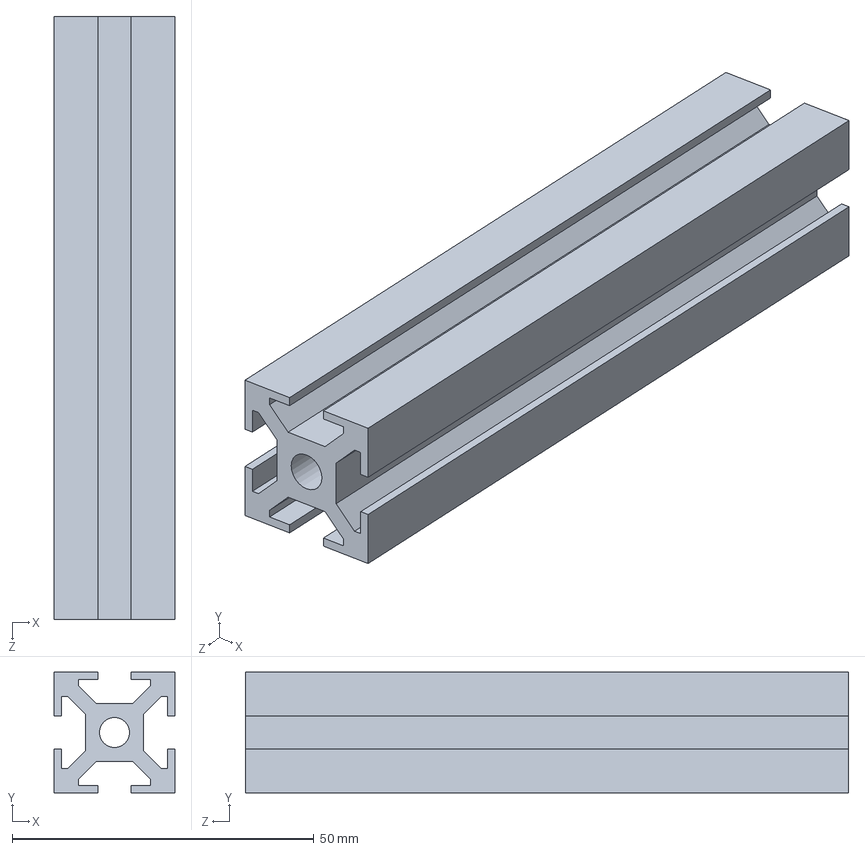
[picture p74: CAD file, 2013-05-11]
sources/solidworks/Profil_Alu_20x20_100mm.SLDPRT
20.0 x 20.0 x 100.0 mm
