Slicit/Roxanne/sources/solidworks/Pulley.SLDPRT

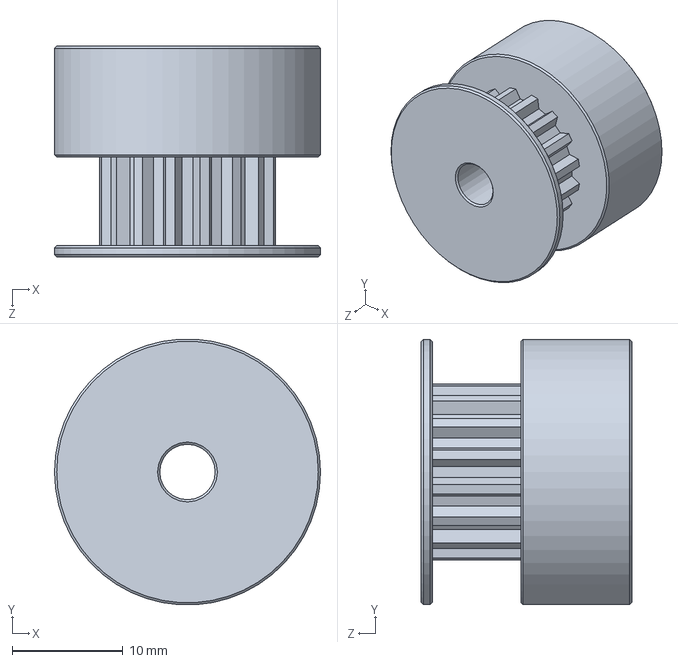
[picture p75: CAD file, 2013-05-11]
sources/solidworks/Pulley.SLDPRT
24.0 x 24.0 x 19.0 mm
