Slicit/Roxanne/sources/solidworks/Profil_Alu_20x20_540mm.SLDPRT

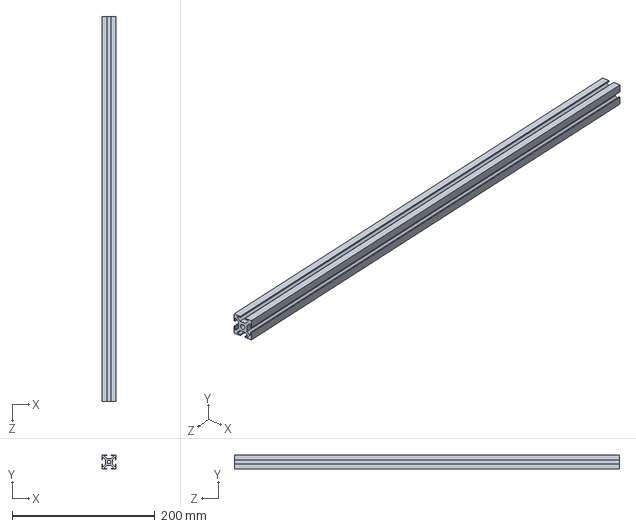
[picture p76: CAD file, 2013-05-11]
sources/solidworks/Profil_Alu_20x20_540mm.SLDPRT
20.0 x 20.0 x 540.0 mm
