Slicit/Roxanne/sources/solidworks/Axe_Guide_140mm.SLDPRT

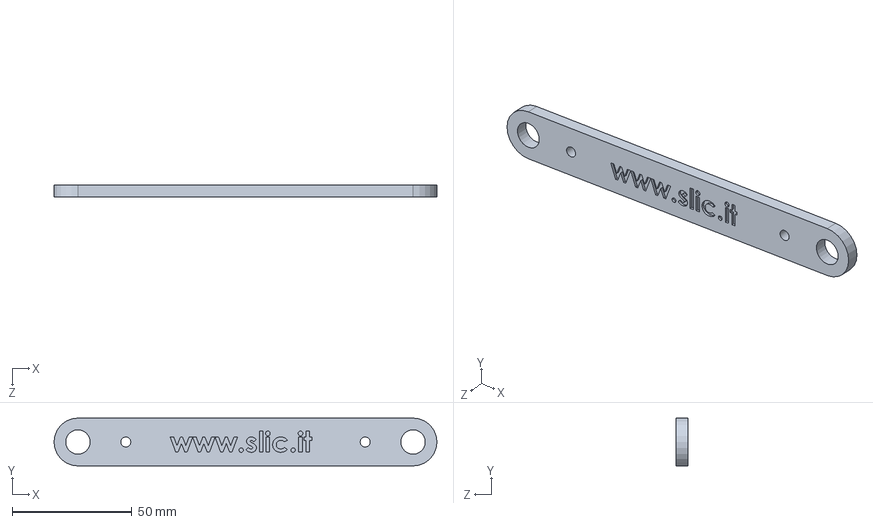
[picture p77: CAD file, 2013-05-11]
sources/solidworks/Axe_Guide_140mm.SLDPRT
160.0 x 20.0 x 5.00 mm
