Slicit/Roxanne/sources/solidworks/Axe_Guide_140mm_Bearing.SLDPRT

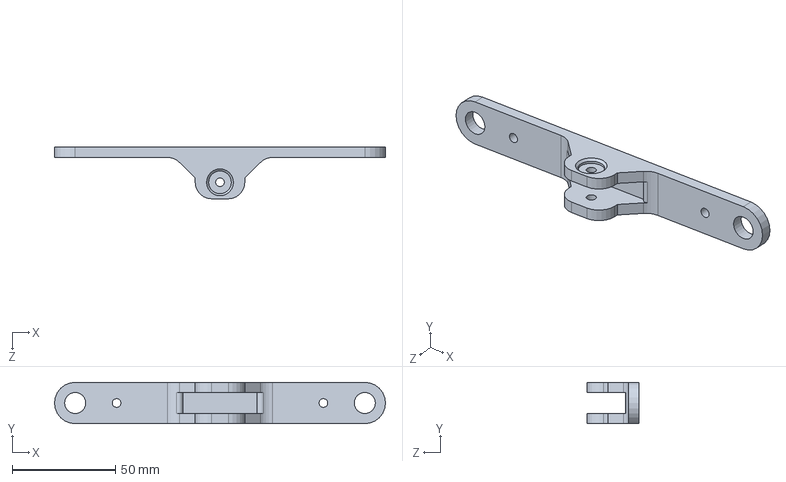
[picture p78: CAD file, 2013-05-11]
sources/solidworks/Axe_Guide_140mm_Bearing.SLDPRT
160.0 x 20.0 x 25.0 mm
