Slicit/Roxanne/sources/solidworks/Angle_2020.SLDPRT

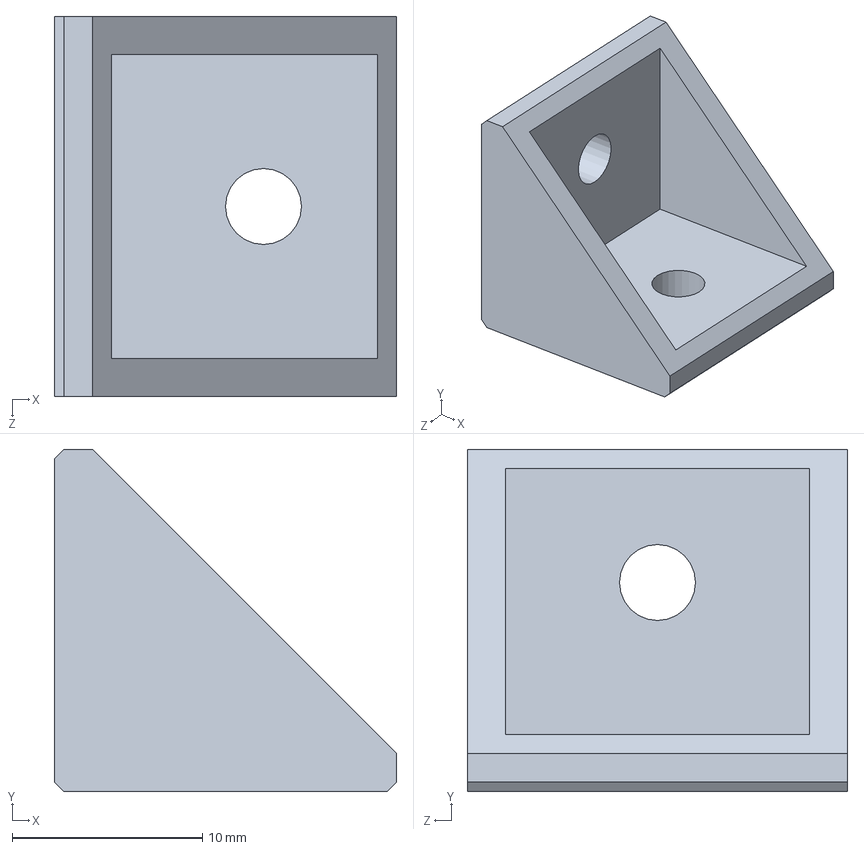
[picture p79: CAD file, 2013-05-11]
sources/solidworks/Angle_2020.SLDPRT
18.0 x 18.0 x 20.0 mm
