Slicit/Roxanne/sources/solidworks/Profil_Alu_20x20_200mm.SLDPRT

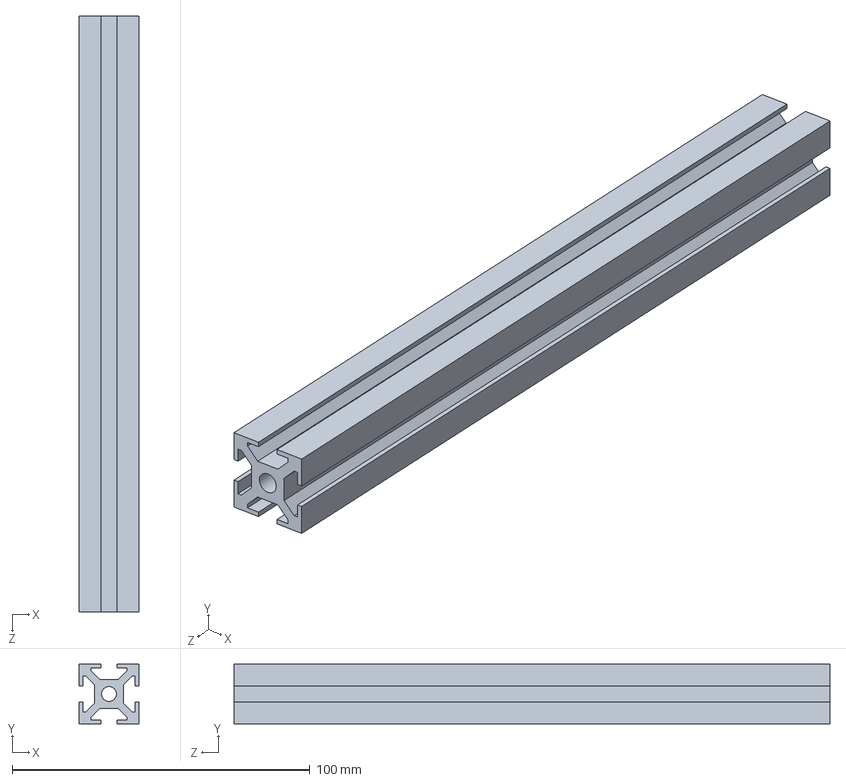
[picture p80: CAD file, 2013-05-11]
sources/solidworks/Profil_Alu_20x20_200mm.SLDPRT
20.0 x 20.0 x 200.0 mm
