Slicit/Roxanne/sources/solidworks/Profil_Alu_20x20_440mm.SLDPRT

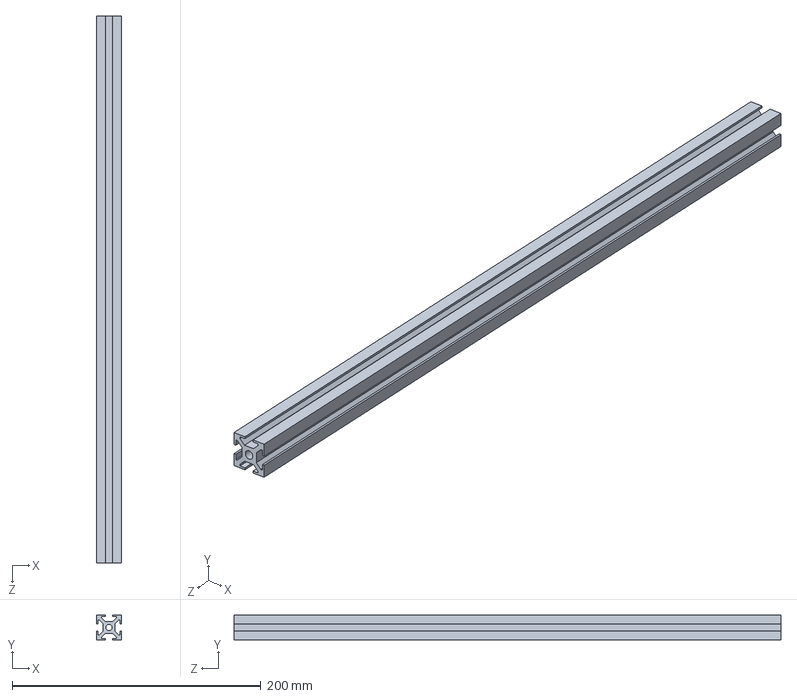
[picture p81: CAD file, 2013-05-11]
sources/solidworks/Profil_Alu_20x20_440mm.SLDPRT
20.0 x 20.0 x 440.0 mm
