Slicit/Roxanne/sources/solidworks/6mm_Threaded_Rod_Simple.SLDPRT

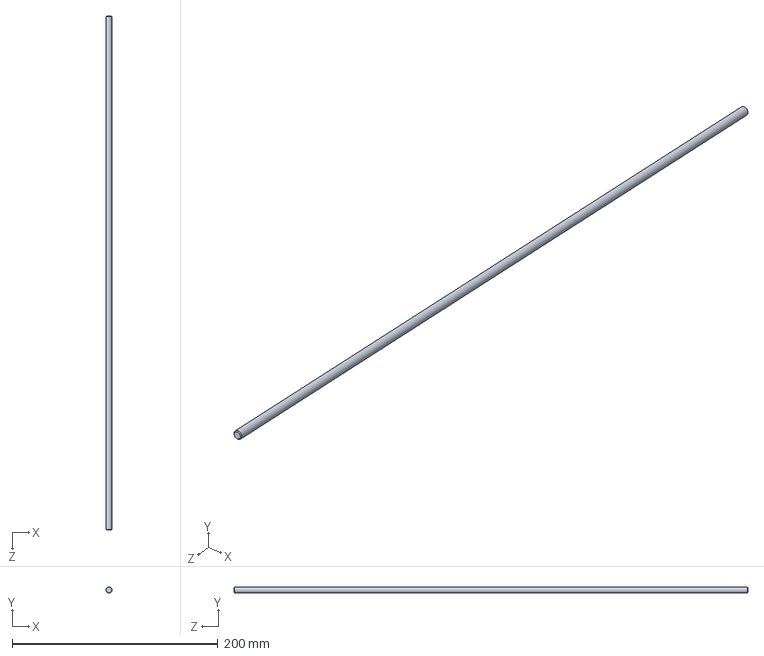
[picture p82: CAD file, 2013-05-11]
sources/solidworks/6mm_Threaded_Rod_Simple.SLDPRT
6.00 x 6.00 x 500.0 mm
