Slicit/Roxanne/sources/solidworks/Aluminium_Bed.SLDPRT

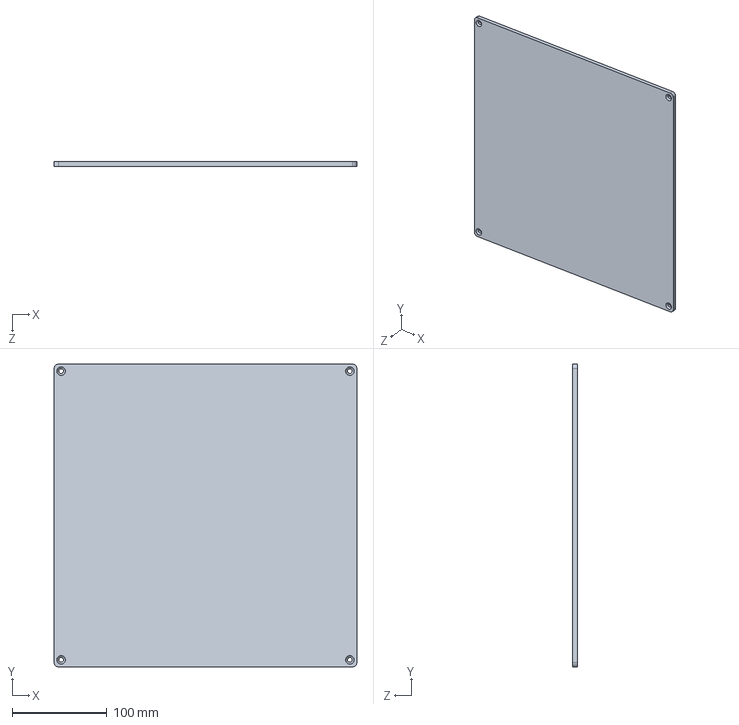
[picture p83: CAD file, 2013-05-11]
sources/solidworks/Aluminium_Bed.SLDPRT
320.0 x 320.0 x 5.00 mm
