Slicit/Roxanne/sources/solidworks/Rod_500mm.SLDPRT

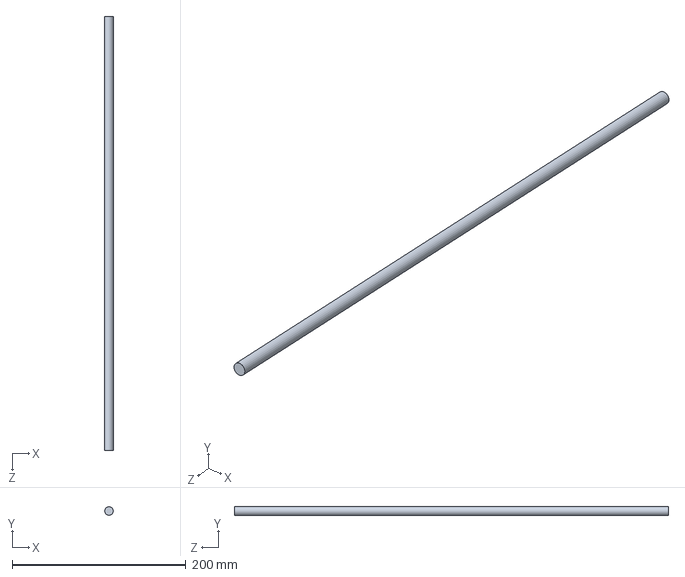
[picture p84: CAD file, 2013-05-11]
sources/solidworks/Rod_500mm.SLDPRT
10.0 x 10.0 x 500.0 mm
