Slicit/Roxanne/sources/solidworks/Direct_Drive_Extruder_Jhead_Vertical_i3.SLDPRT

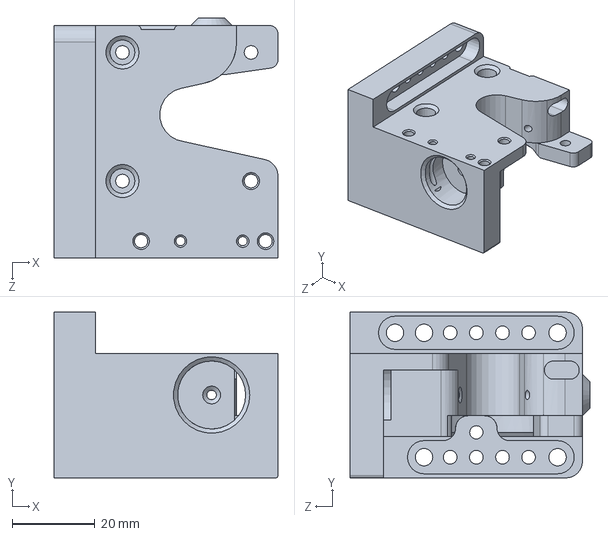
[picture p85: CAD file, 2013-05-11]
sources/solidworks/Direct_Drive_Extruder_Jhead_Vertical_i3.SLDPRT
54.0 x 40.0 x 57.8 mm
