Slicit/Roxanne/sources/solidworks/Stamp_Foot.SLDPRT

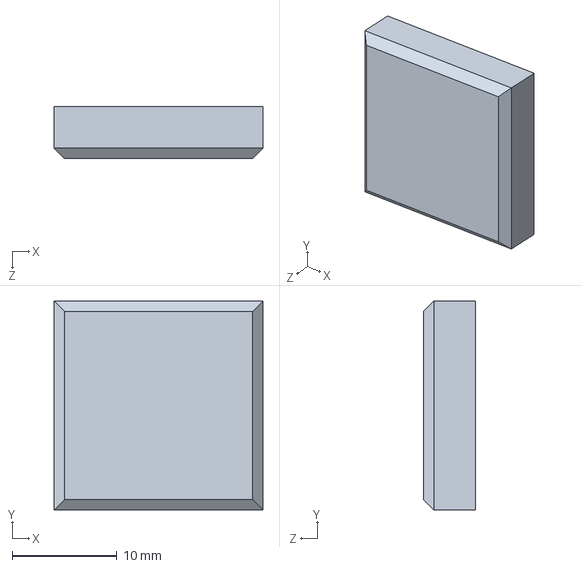
[picture p86: CAD file, 2013-05-11]
sources/solidworks/Stamp_Foot.SLDPRT
20.0 x 20.0 x 5.00 mm
