Slicit/Roxanne/sources/solidworks/Profil_Alu_20x20_340mm.SLDPRT

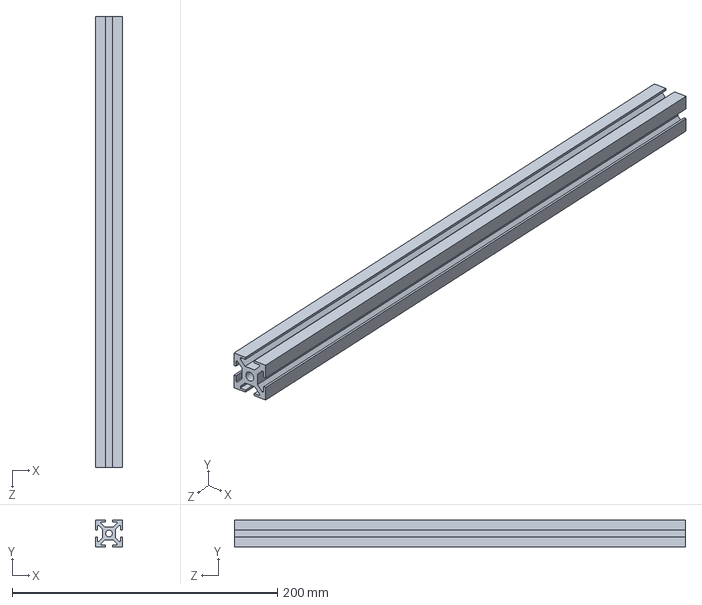
[picture p87: CAD file, 2013-05-11]
sources/solidworks/Profil_Alu_20x20_340mm.SLDPRT
20.0 x 20.0 x 340.0 mm
