Slicit/Roxanne/sources/solidworks/Z_Coupler_5_6.SLDPRT

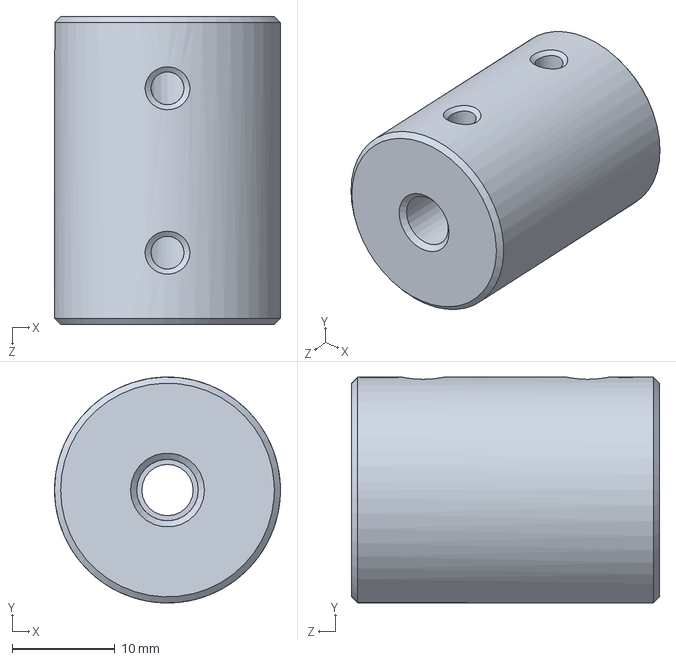
[picture p88: CAD file, 2013-05-11]
sources/solidworks/Z_Coupler_5_6.SLDPRT
22.0 x 22.0 x 30.0 mm
