Slicit/Roxanne/sources/solidworks/Profil_Alu_20x20_400mm.SLDPRT

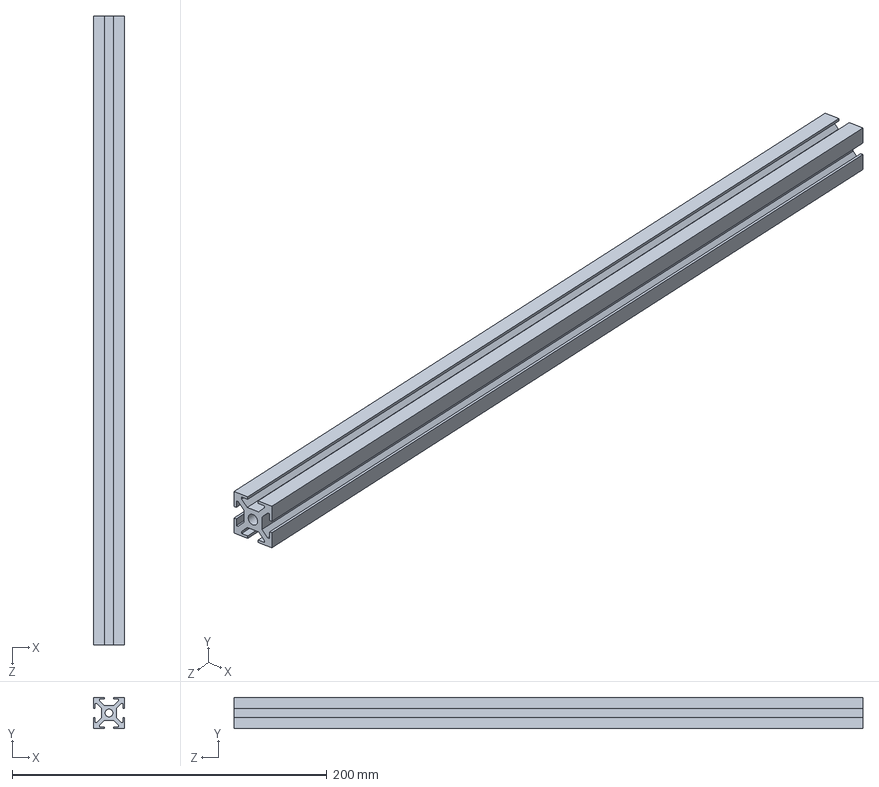
[picture p89: CAD file, 2013-05-11]
sources/solidworks/Profil_Alu_20x20_400mm.SLDPRT
20.0 x 20.0 x 400.0 mm
